impatrq/Pleper/Documentos Proyecto/CV Alumnos/CV Santiago_Alejandro_Tejeda.pdf

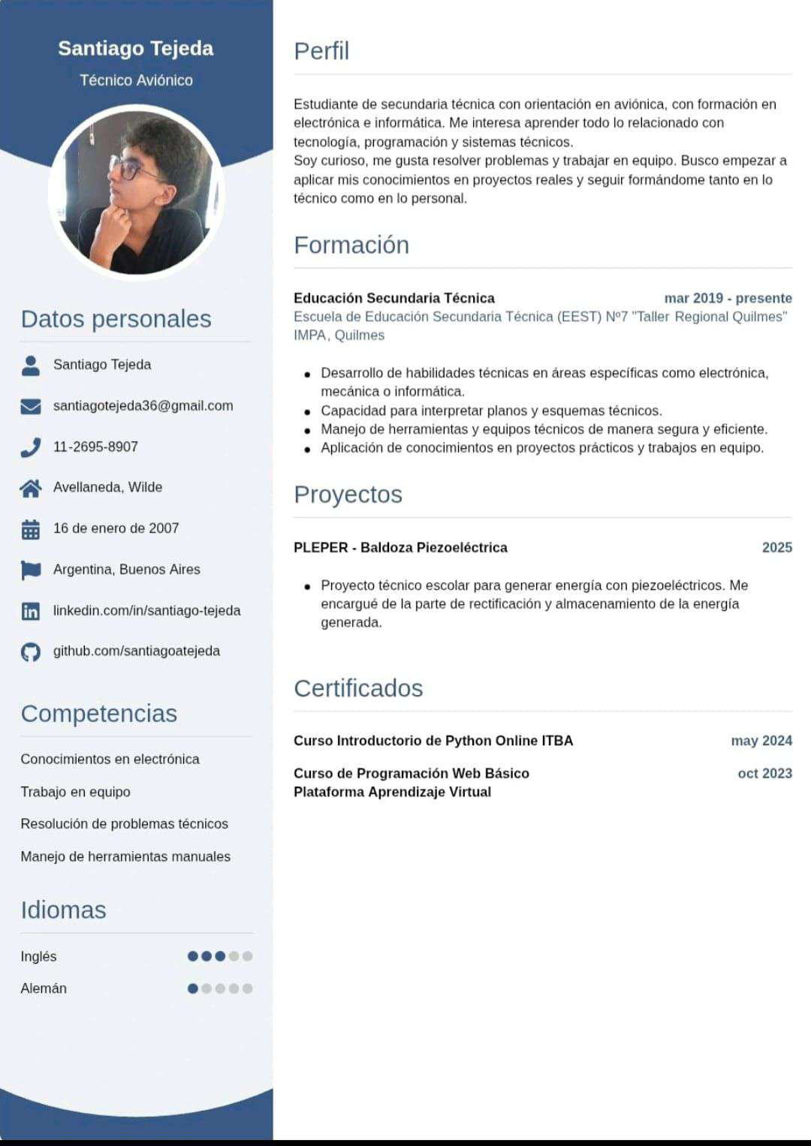
[picture p9: page 1]
