impatrq/Pleper/Documentos Proyecto/CV Alumnos/CV Ignacio Garcia Louzan.pdf

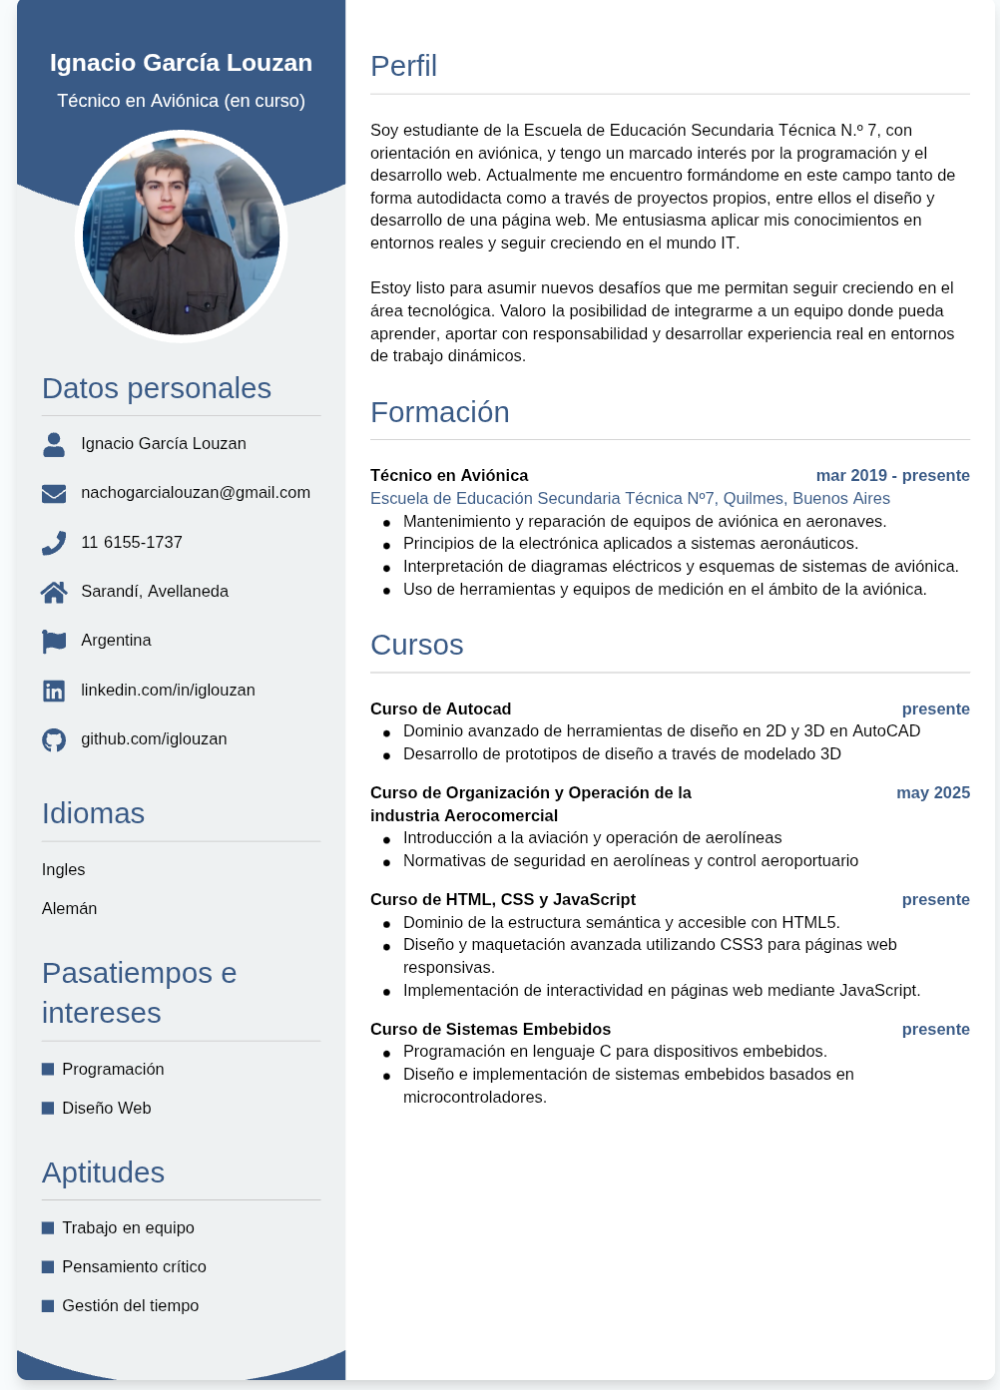
[picture p10: page 1]
