impatrq/Pleper/Diseño de placas/Diseño 3D/Banco de Capacitores Vista 1.png

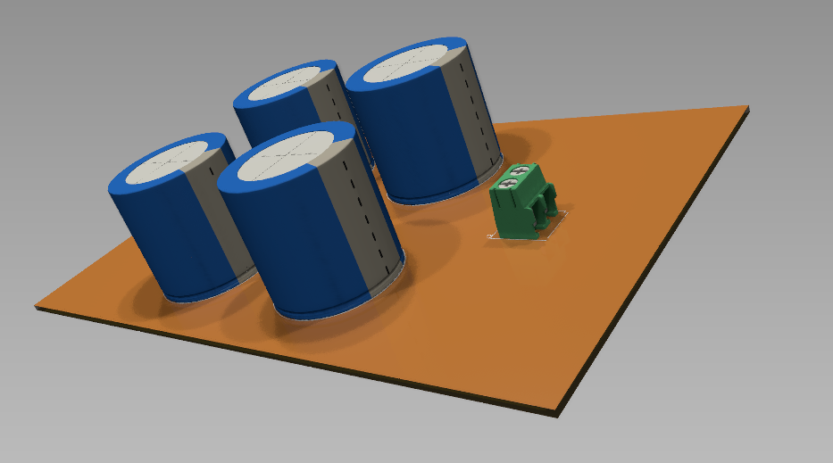
Diseño de placas/Diseño 3D/Banco de Capacitores Vista 1.png
