impatrq/Pleper/Diseño de placas/Diseño 3D/Banco de Capacitores Vista 3.png

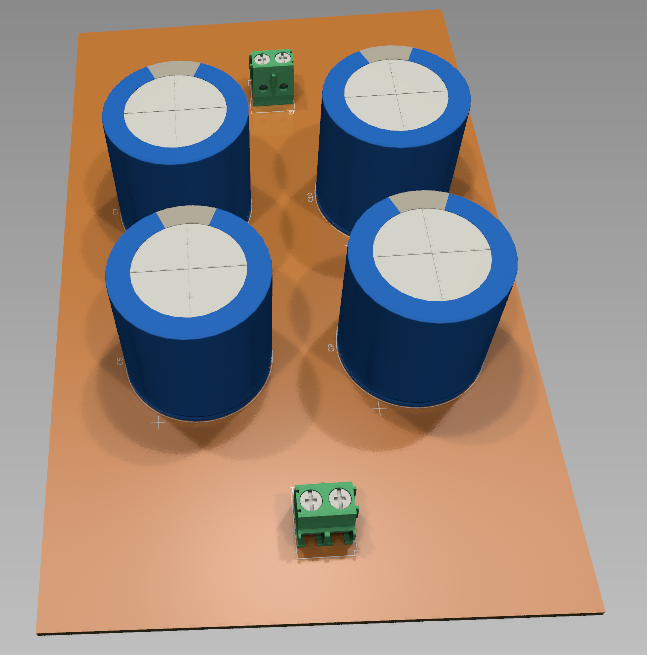
Diseño de placas/Diseño 3D/Banco de Capacitores Vista 3.png
