impatrq/Pleper/Diseño de placas/Diseño 3D/Placa rectificadora Vista 3.png

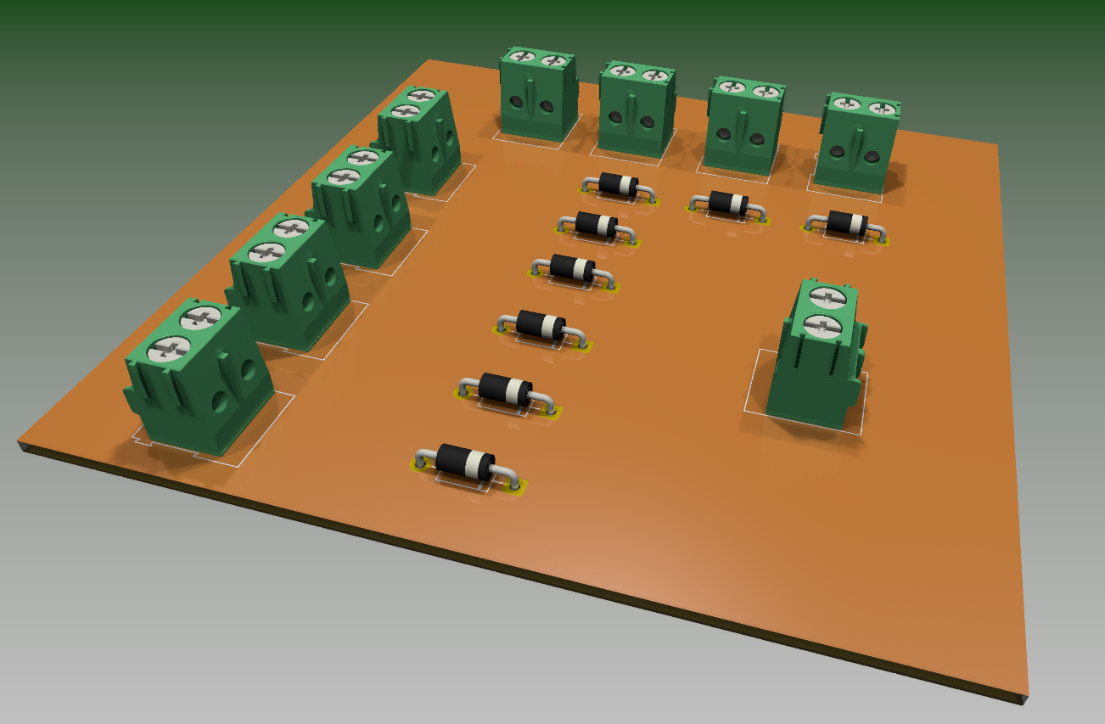
Diseño de placas/Diseño 3D/Placa rectificadora Vista 3.png
