impatrq/Pleper/Diseño de placas/Placa rectificadora/Boceto de rectificadora/20250923_140442.jpg

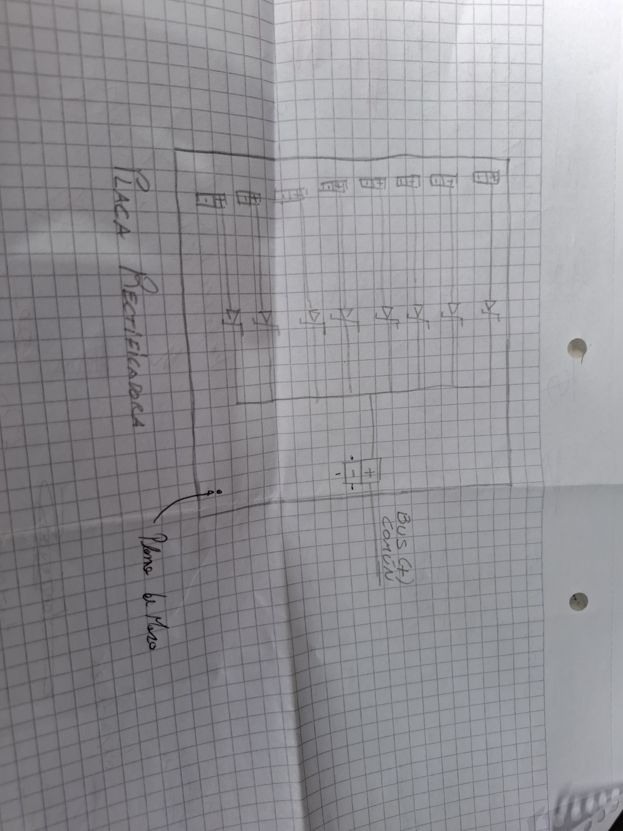
Diseño de placas/Placa rectificadora/Boceto de rectificadora/20250923_140442.jpg
