impatrq/Pleper/Diseño de placas/Placa rectificadora/Boceto de rectificadora/Esquematico placa rectificadora.png

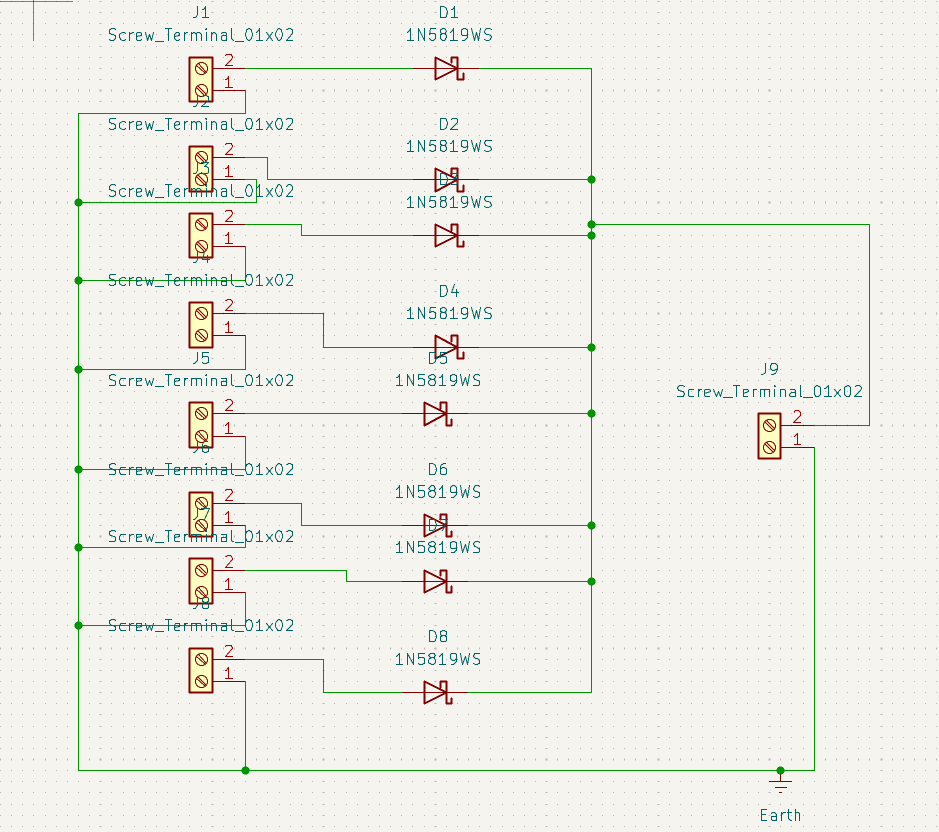
Diseño de placas/Placa rectificadora/Boceto de rectificadora/Esquematico placa rectificadora.png
