impatrq/Pleper/Diseño y modelos 3D/Imagenes de AutoCad/Captura de pantalla 2025-10-30 134244.png

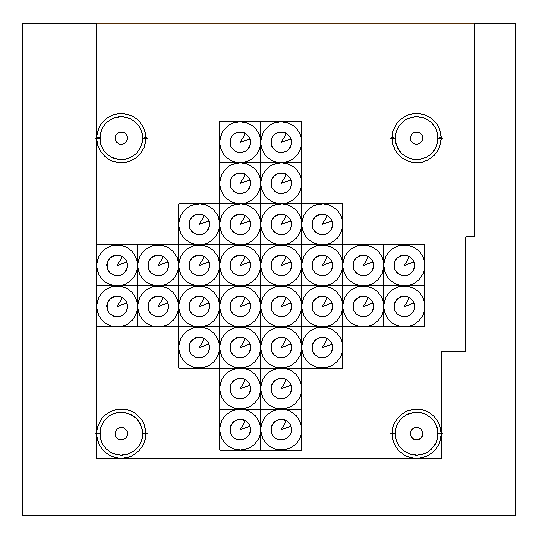
Diseño y modelos 3D/Imagenes de AutoCad/Captura de pantalla 2025-10-30 134244.png
