impatrq/Pleper/Diseño y modelos 3D/Imagenes de AutoCad/Vista conceptual 1.png

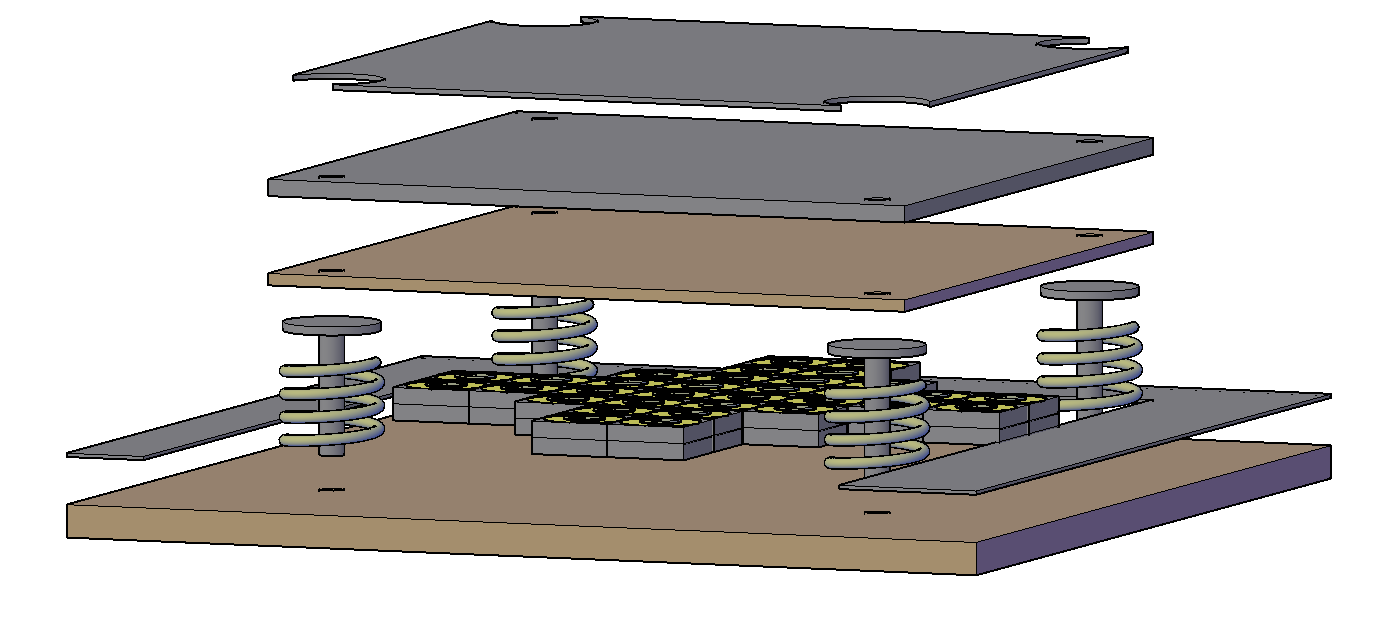
Diseño y modelos 3D/Imagenes de AutoCad/Vista conceptual 1.png
