impatrq/Pleper/Diseño y modelos 3D/Imagenes de AutoCad/Vista conceptual 5.png

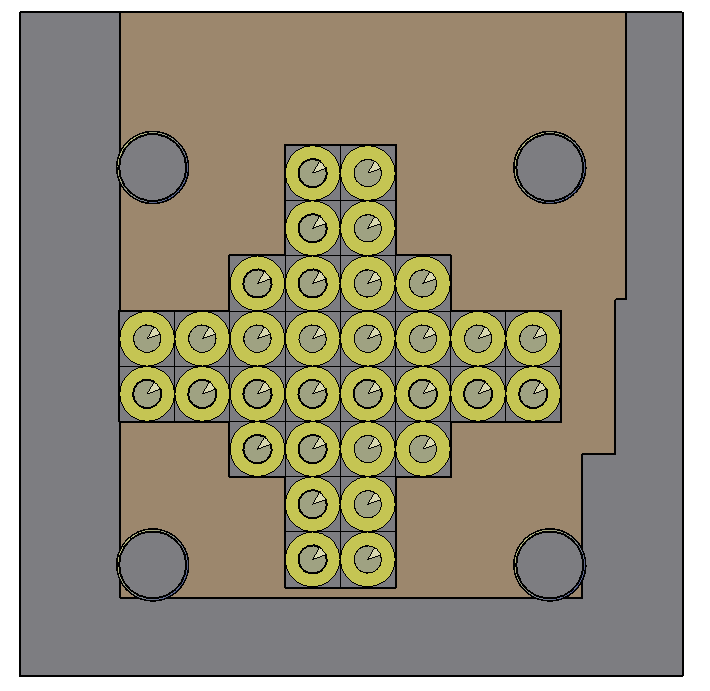
Diseño y modelos 3D/Imagenes de AutoCad/Vista conceptual 5.png
