impatrq/Pleper/Diseño y modelos 3D/Imagenes de AutoCad/Vista Isométrica 2.png

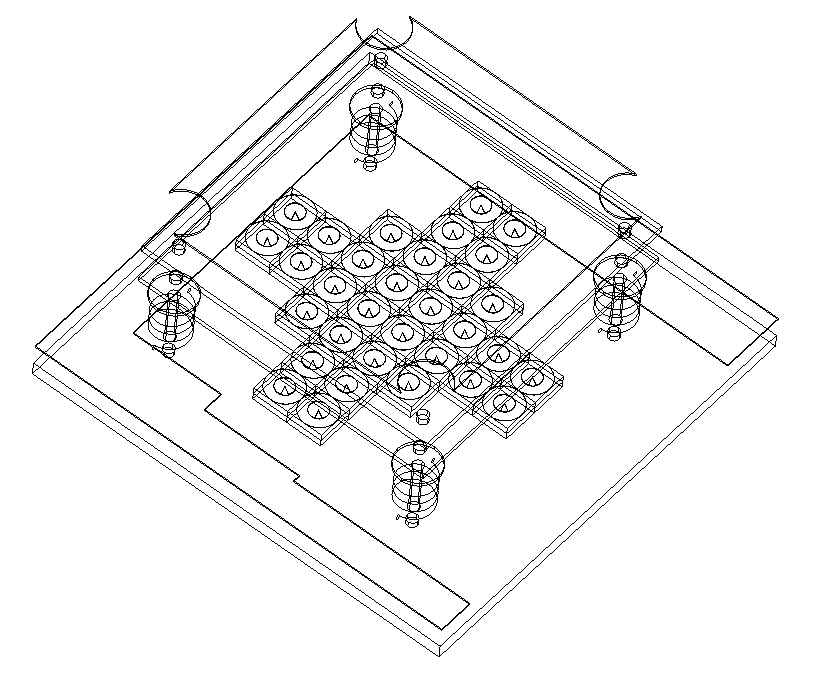
Diseño y modelos 3D/Imagenes de AutoCad/Vista Isométrica 2.png
