impatrq/Pleper/Diseño y modelos 3D/Imagenes de AutoCad/Vista Isométrica 3.png

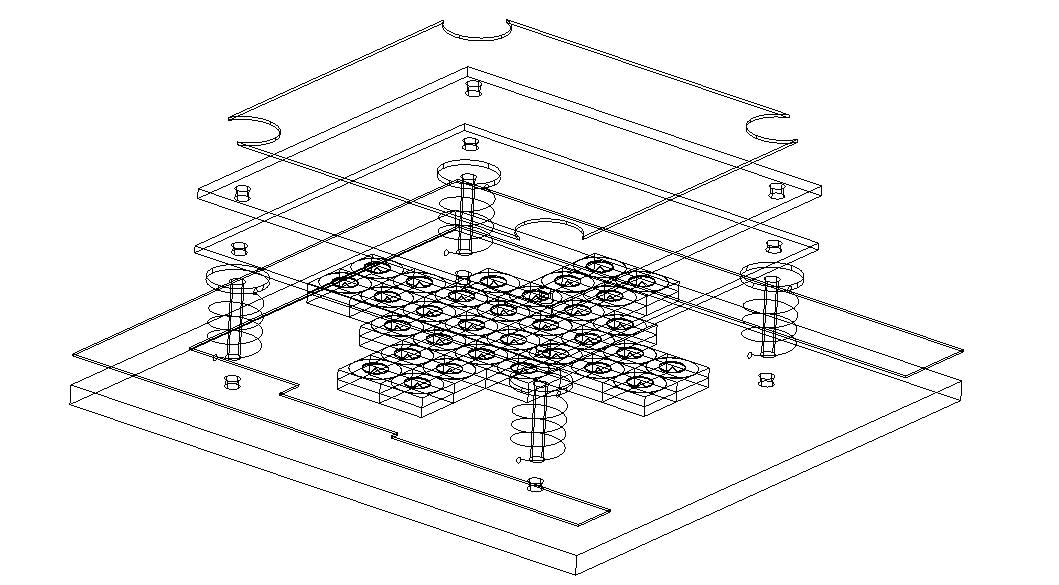
Diseño y modelos 3D/Imagenes de AutoCad/Vista Isométrica 3.png
