impatrq/Pleper/Diseño y modelos 3D/Imagenes de AutoCad/Vista Isométrica prototipo.png

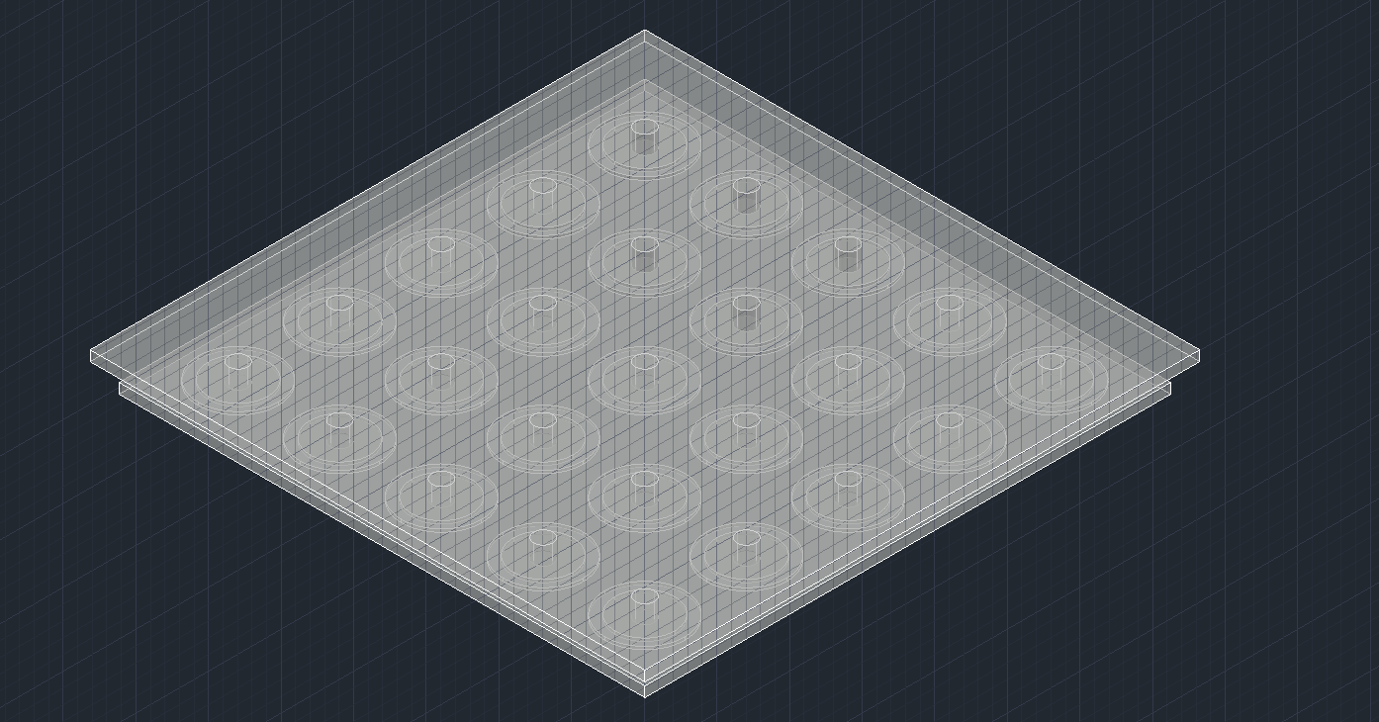
Diseño y modelos 3D/Imagenes de AutoCad/Vista Isométrica prototipo.png
