impatrq/Pleper/Diseño y modelos 3D/Imagenes de AutoCad/Vista realista 4.png

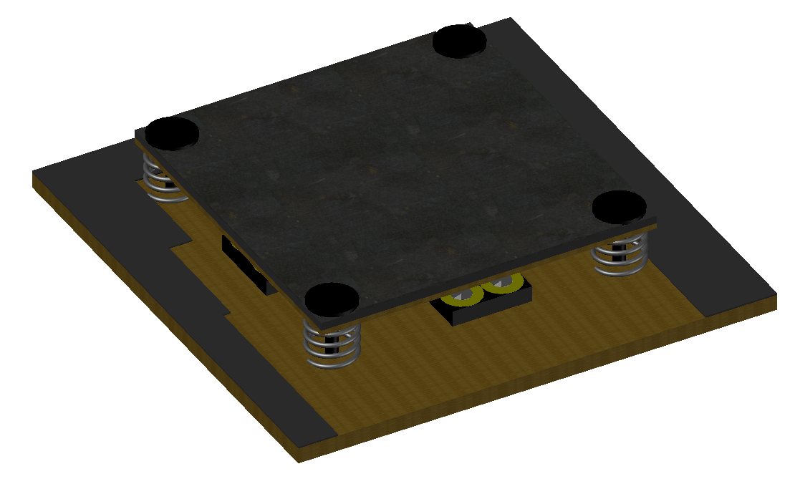
Diseño y modelos 3D/Imagenes de AutoCad/Vista realista 4.png
