impatrq/Pleper/Diseño y modelos 3D/Imagenes de AutoCad/Vista realista 5.png

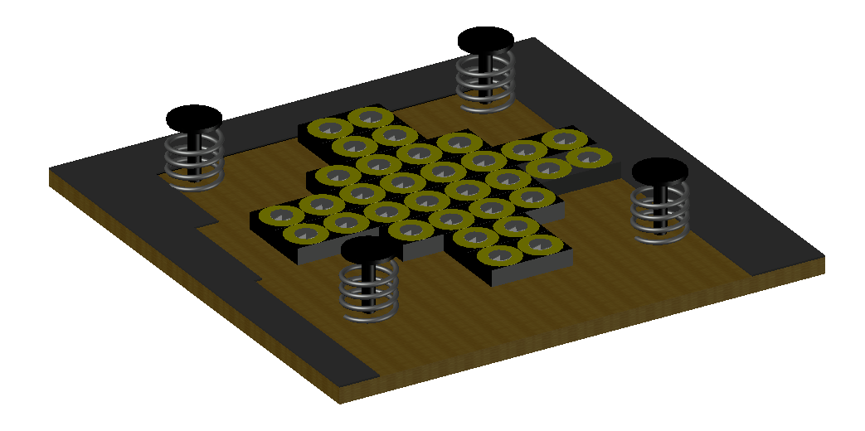
Diseño y modelos 3D/Imagenes de AutoCad/Vista realista 5.png
