impatrq/Pleper/Diseño y modelos 3D/Imagenes de AutoCad/Vista realista.png

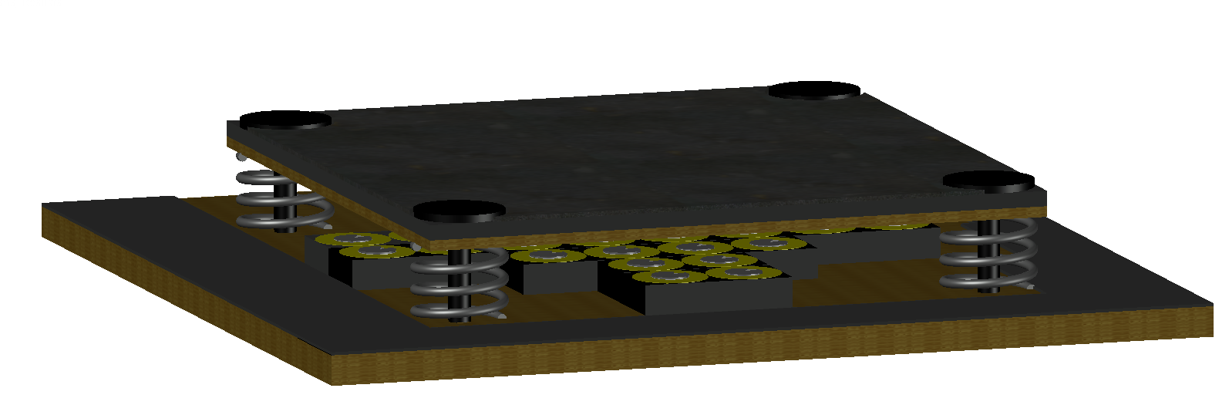
Diseño y modelos 3D/Imagenes de AutoCad/Vista realista.png
