impatrq/Pleper/Diseño y modelos 3D/Imagenes de AutoCad/Vista Superior prototipo.png

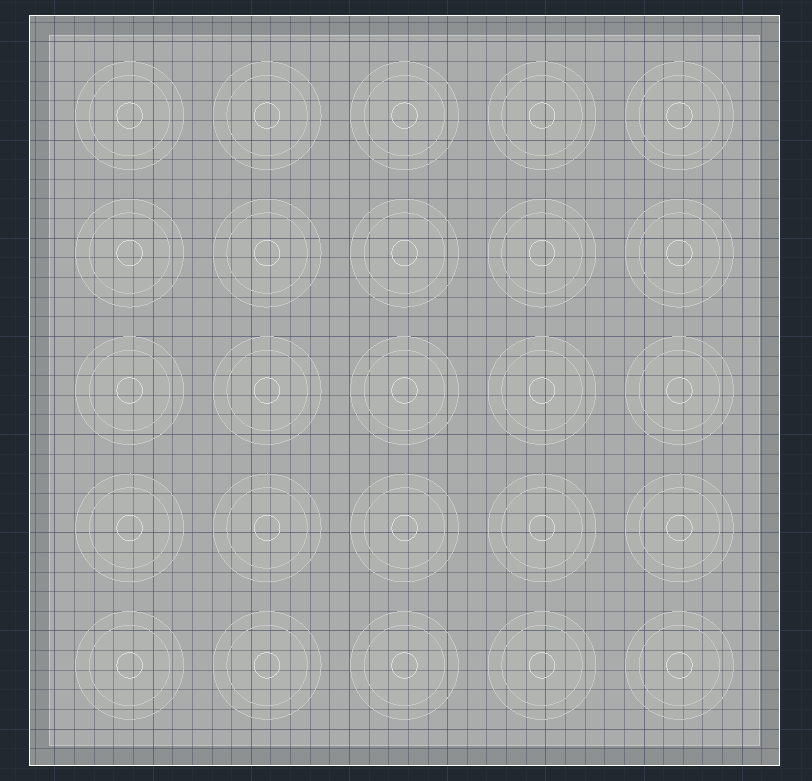
Diseño y modelos 3D/Imagenes de AutoCad/Vista Superior prototipo.png
