impatrq/Pleper/Documentos Proyecto/Video de presentacion/Pisada en prototipo de placa.jpg

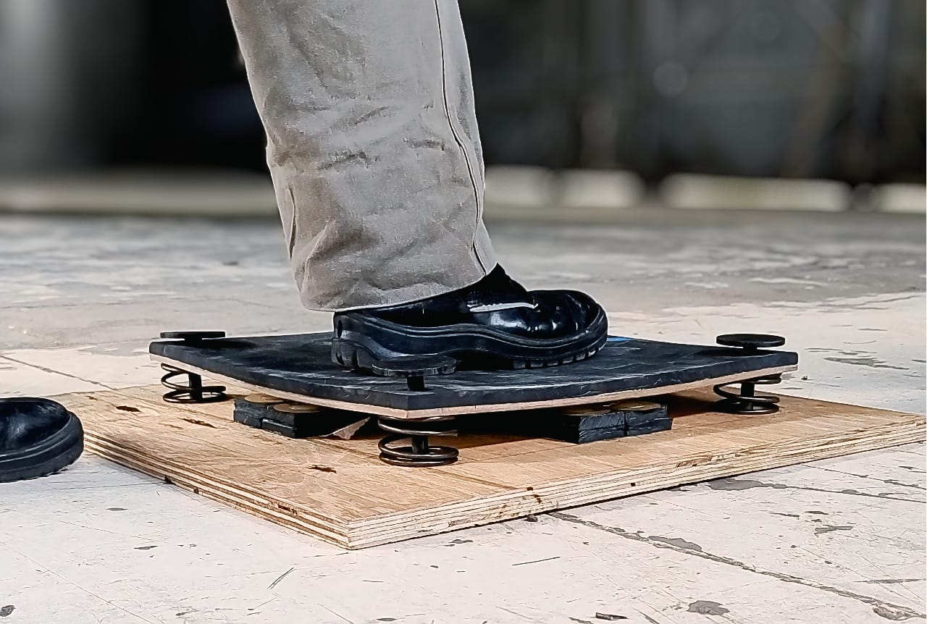
Documentos Proyecto/Video de presentacion/Pisada en prototipo de placa.jpg
