impatrq/Pleper/img/fondo.jpg

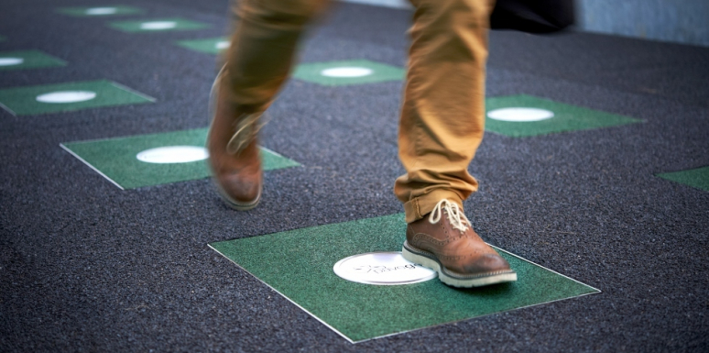
img/fondo.jpg
