impatrq/Pleper/Imágenes Proyecto/Desarrollo/Circuitos/Investigación sobre el circuito de bombeo por carga capacitiva.jpg

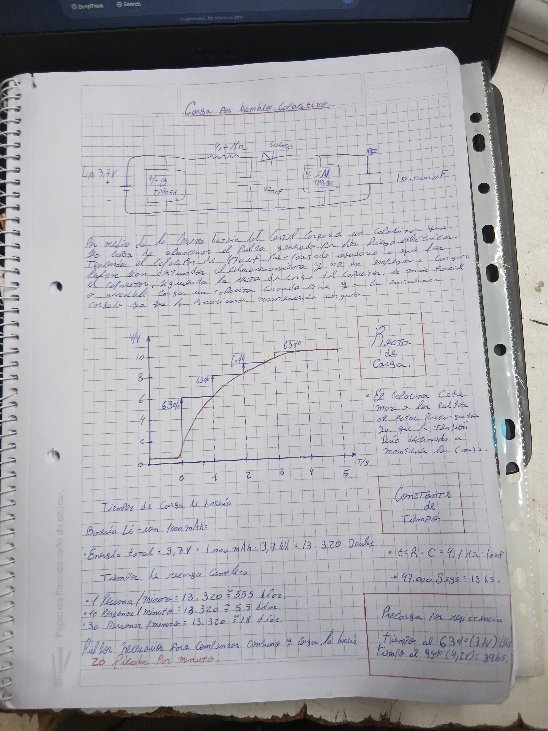
Imágenes Proyecto/Desarrollo/Circuitos/Investigación sobre el circuito de bombeo por carga capacitiva.jpg
