impatrq/Pleper/Imágenes Proyecto/Desarrollo/Circuitos/Primera Versión.jpg

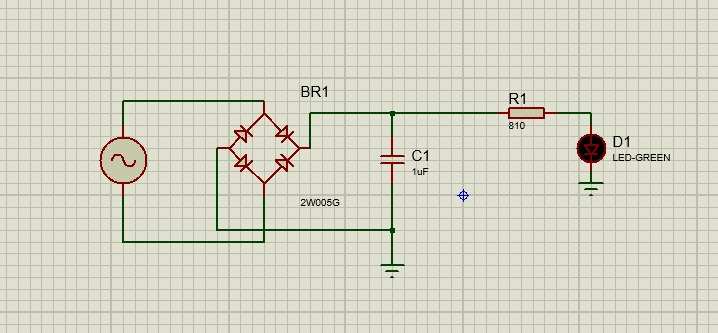
Imágenes Proyecto/Desarrollo/Circuitos/Primera Versión.jpg
