impatrq/Pleper/Imágenes Proyecto/Desarrollo/Circuitos/Simulación seis piezoeléctricos.jpg

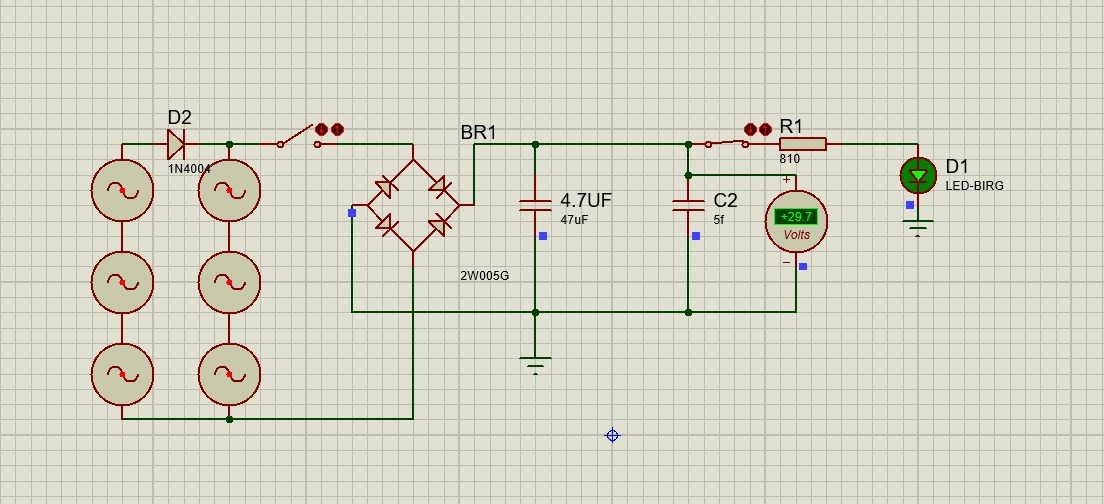
Imágenes Proyecto/Desarrollo/Circuitos/Simulación seis piezoeléctricos.jpg
