impatrq/Pleper/Imágenes Proyecto/Desarrollo/Circuitos/Simulación un piezoeléctrico con rectificación.jpg

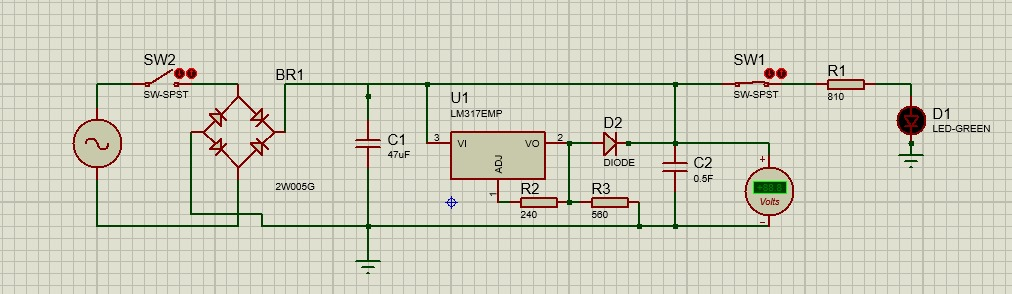
Imágenes Proyecto/Desarrollo/Circuitos/Simulación un piezoeléctrico con rectificación.jpg
