impatrq/Pleper/Imágenes Proyecto/Desarrollo/Imagen de placas/Banco de capacitores PCB.png

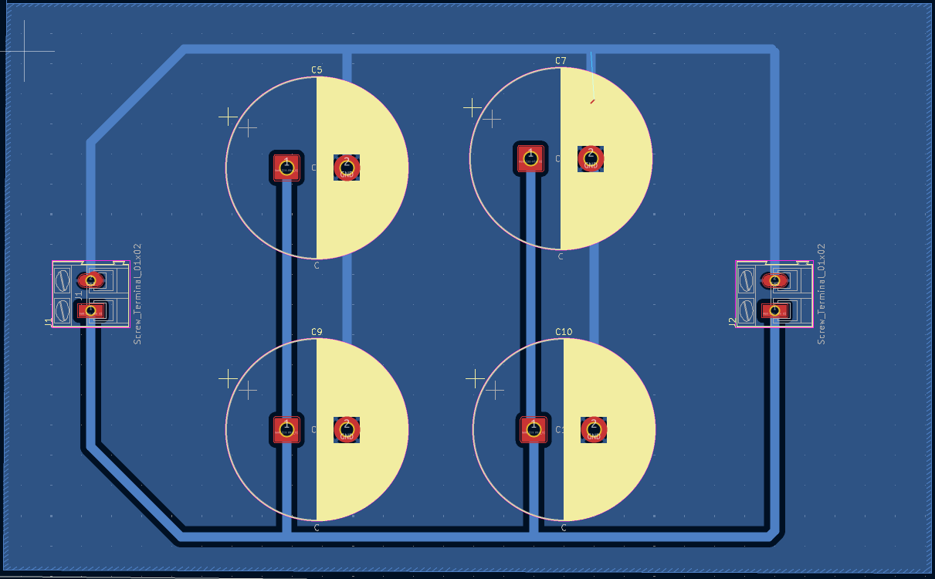
Imágenes Proyecto/Desarrollo/Imagen de placas/Banco de capacitores PCB.png
