impatrq/Pleper/Imágenes Proyecto/Desarrollo/Imagen de placas/Banco de capacitores.jpg

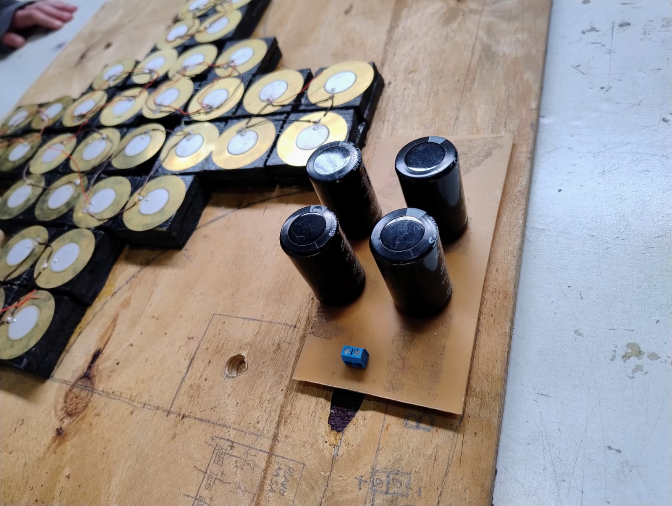
Imágenes Proyecto/Desarrollo/Imagen de placas/Banco de capacitores.jpg
