impatrq/Pleper/Imágenes Proyecto/Desarrollo/Imagen de placas/Banco de capacitores.png

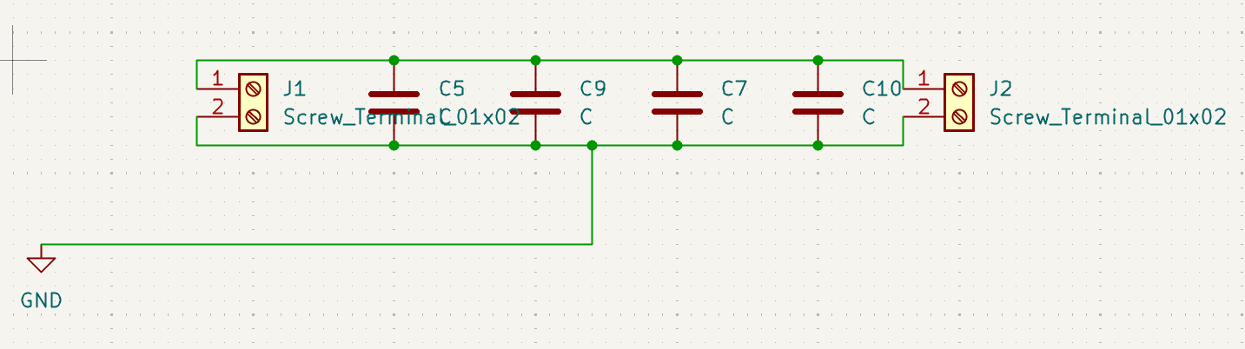
Imágenes Proyecto/Desarrollo/Imagen de placas/Banco de capacitores.png
