impatrq/Pleper/Imágenes Proyecto/Desarrollo/Imagen de placas/Circuito de la baldosa de carga por bombeo capacitivo.jpg

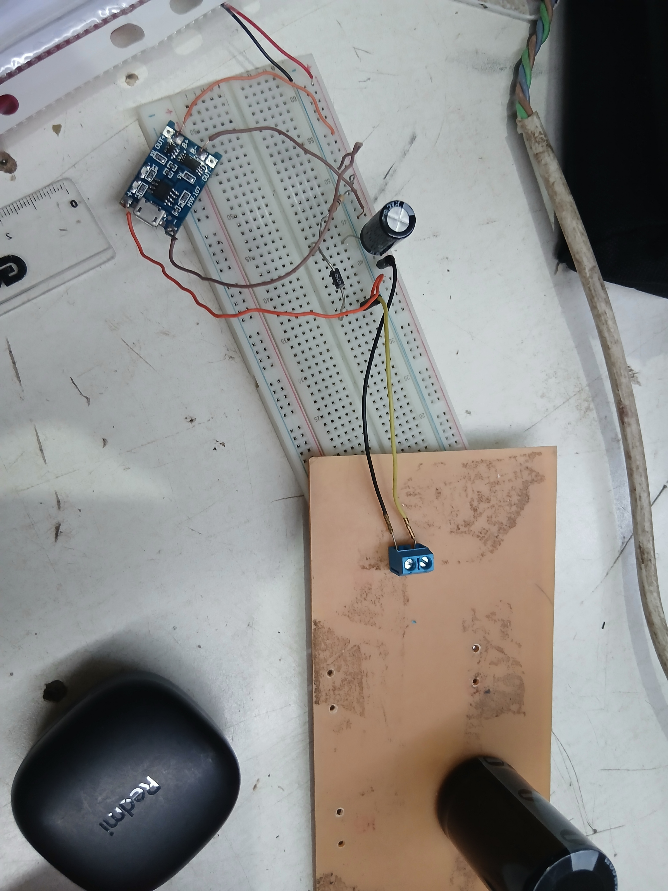
Imágenes Proyecto/Desarrollo/Imagen de placas/Circuito de la baldosa de carga por bombeo capacitivo.jpg
