impatrq/Pleper/Imágenes Proyecto/Desarrollo/Imagen de placas/Placa rectificadora PCB.png

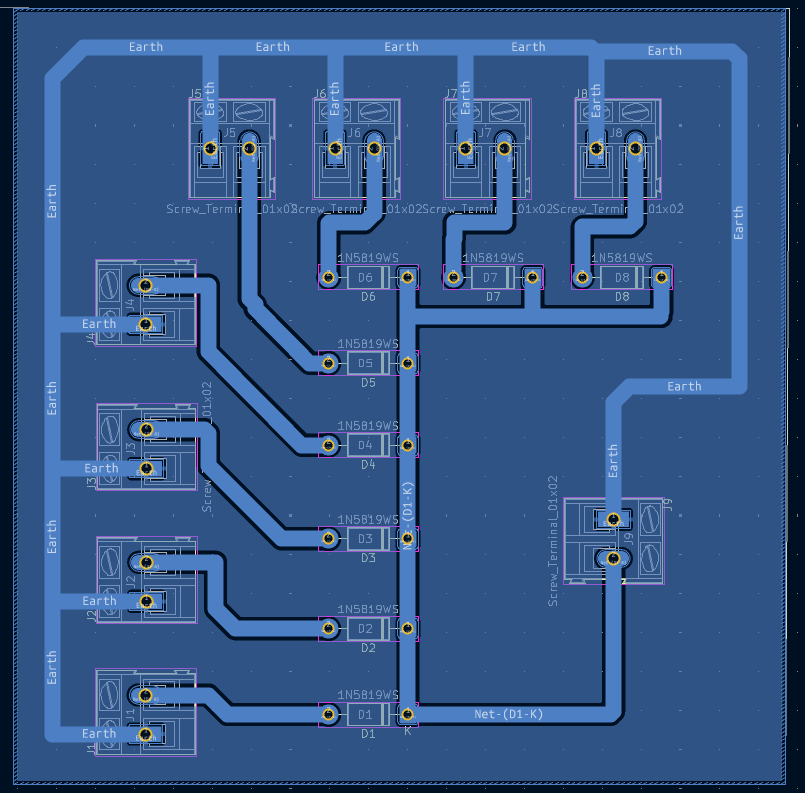
Imágenes Proyecto/Desarrollo/Imagen de placas/Placa rectificadora PCB.png
