impatrq/Pleper/Imágenes Proyecto/Desarrollo/Mediciones/Medicion de 1 tope en un grupo.jpeg

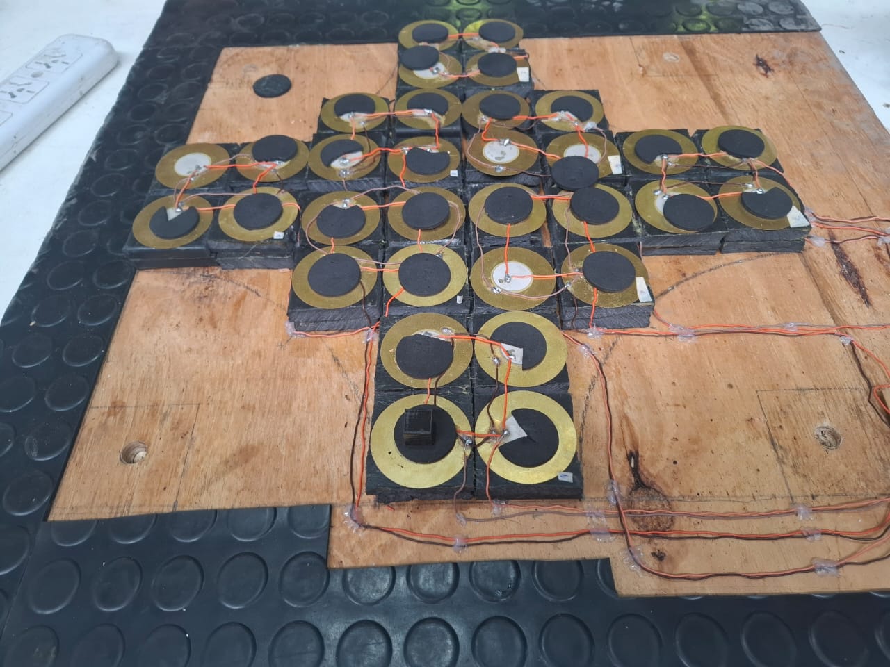
Imágenes Proyecto/Desarrollo/Mediciones/Medicion de 1 tope en un grupo.jpeg
