impatrq/Pleper/Imágenes Proyecto/Desarrollo/Mediciones/Medicion de 2  topes en un grupo.jpeg

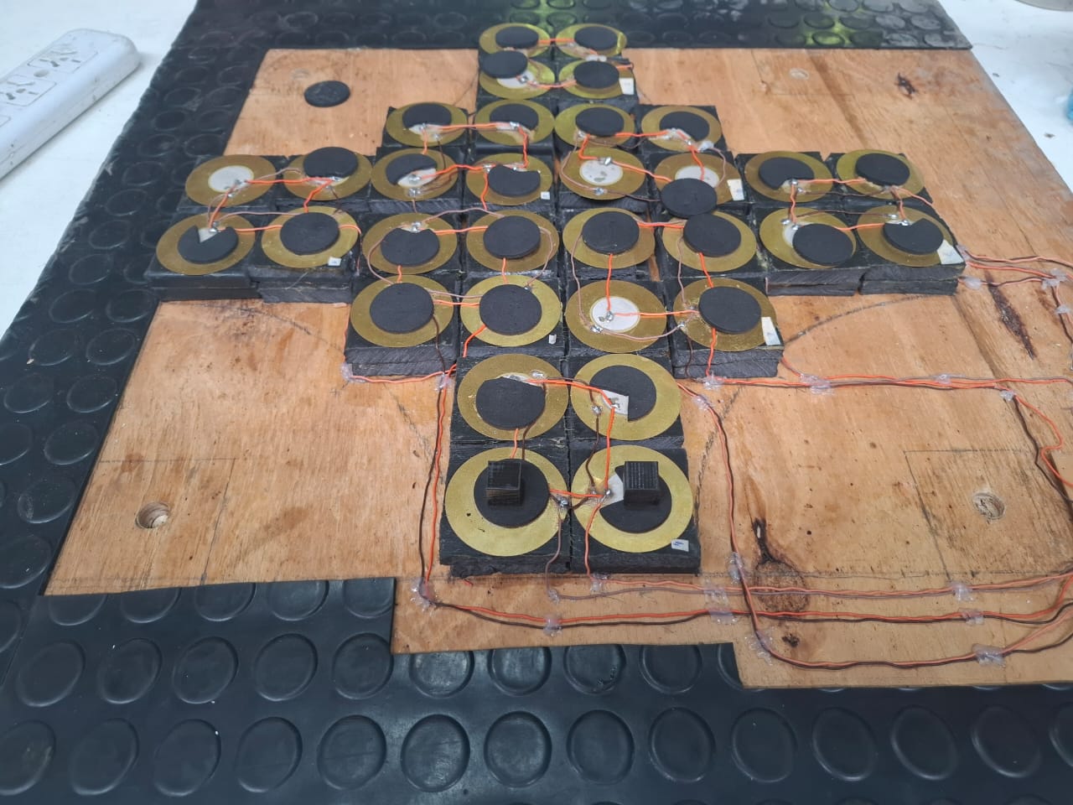
Imágenes Proyecto/Desarrollo/Mediciones/Medicion de 2 topes en un grupo.jpeg
