impatrq/Pleper/Imágenes Proyecto/Desarrollo/Mediciones/Medicion de 3 topes en un grupo.jpeg

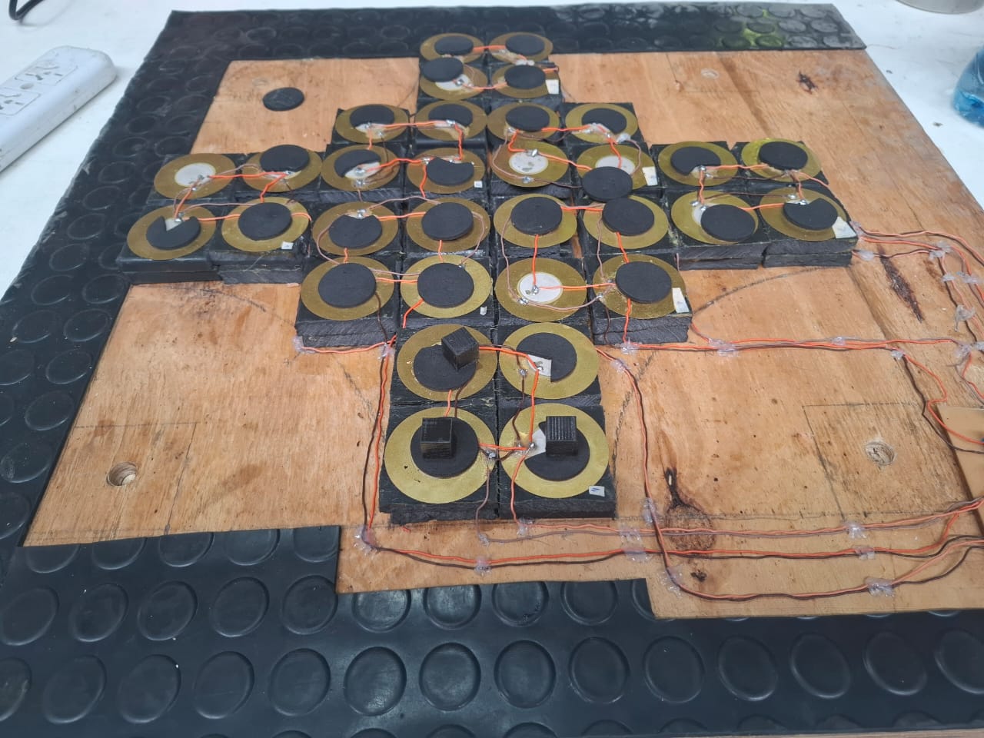
Imágenes Proyecto/Desarrollo/Mediciones/Medicion de 3 topes en un grupo.jpeg
