impatrq/Pleper/Imágenes Proyecto/Desarrollo/Mediciones/Medicion de 4 topes en un grupo.jpeg

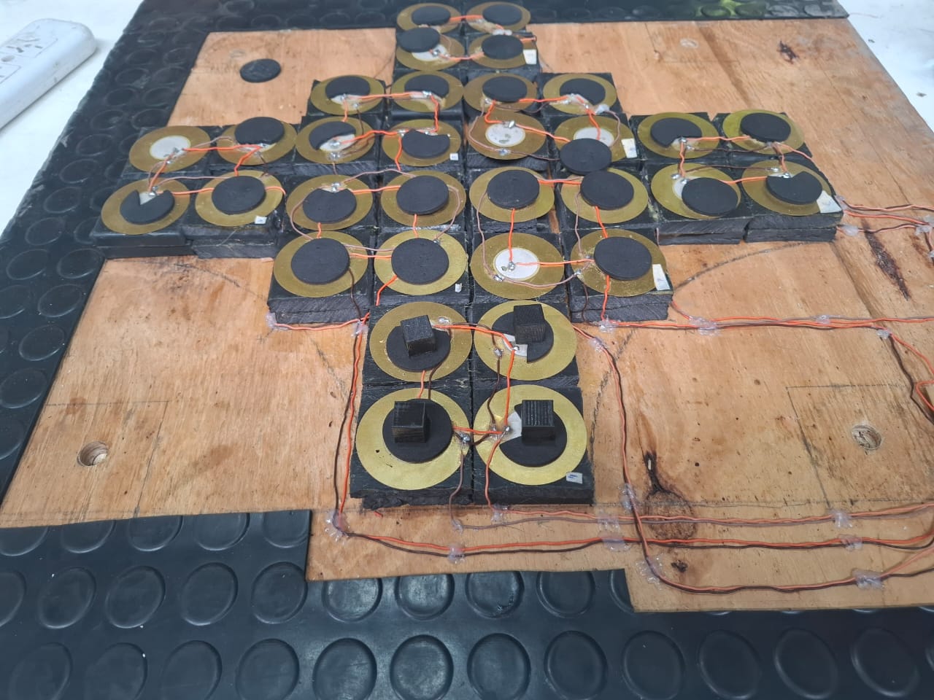
Imágenes Proyecto/Desarrollo/Mediciones/Medicion de 4 topes en un grupo.jpeg
