impatrq/Pleper/Imágenes Proyecto/Desarrollo/Mediciones/Medicion de un tope en cada esquina.jpeg

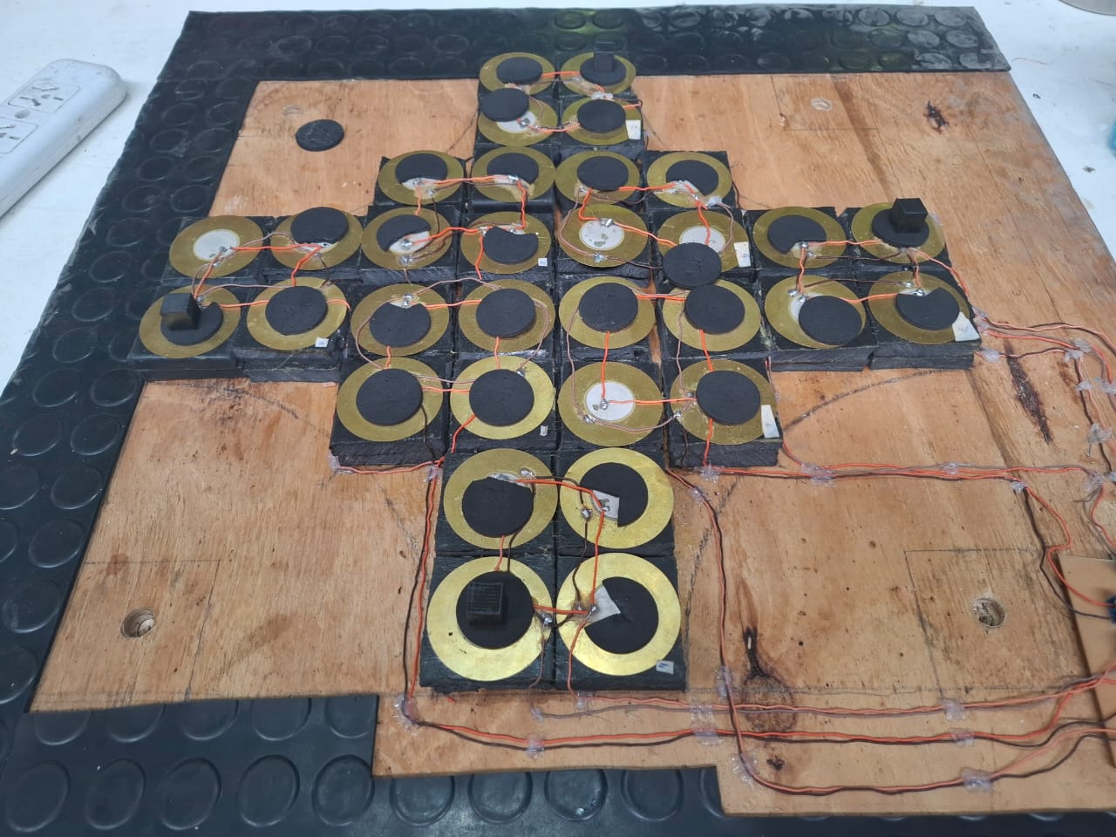
Imágenes Proyecto/Desarrollo/Mediciones/Medicion de un tope en cada esquina.jpeg
