impatrq/Pleper/Imágenes Proyecto/Desarrollo/Mediciones/Medicion del corte de alfombra de caucho para los topes.jpg

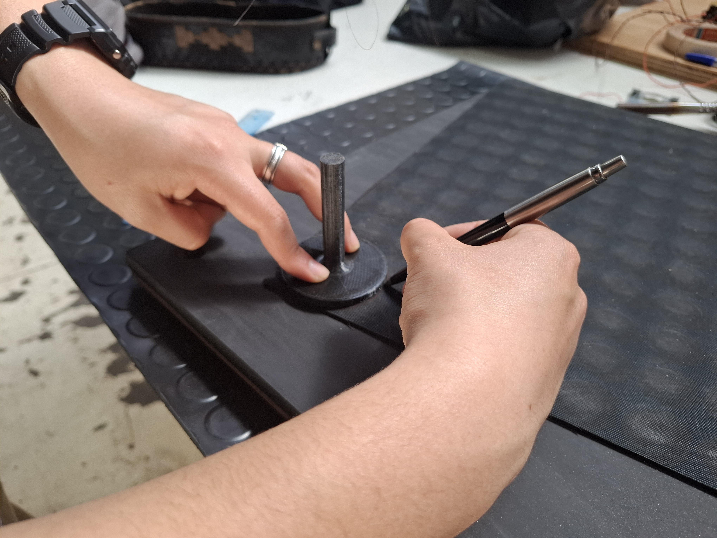
Imágenes Proyecto/Desarrollo/Mediciones/Medicion del corte de alfombra de caucho para los topes.jpg
