impatrq/Pleper/Imágenes Proyecto/Desarrollo/Mediciones/Mediciones en el prototipo.jpg

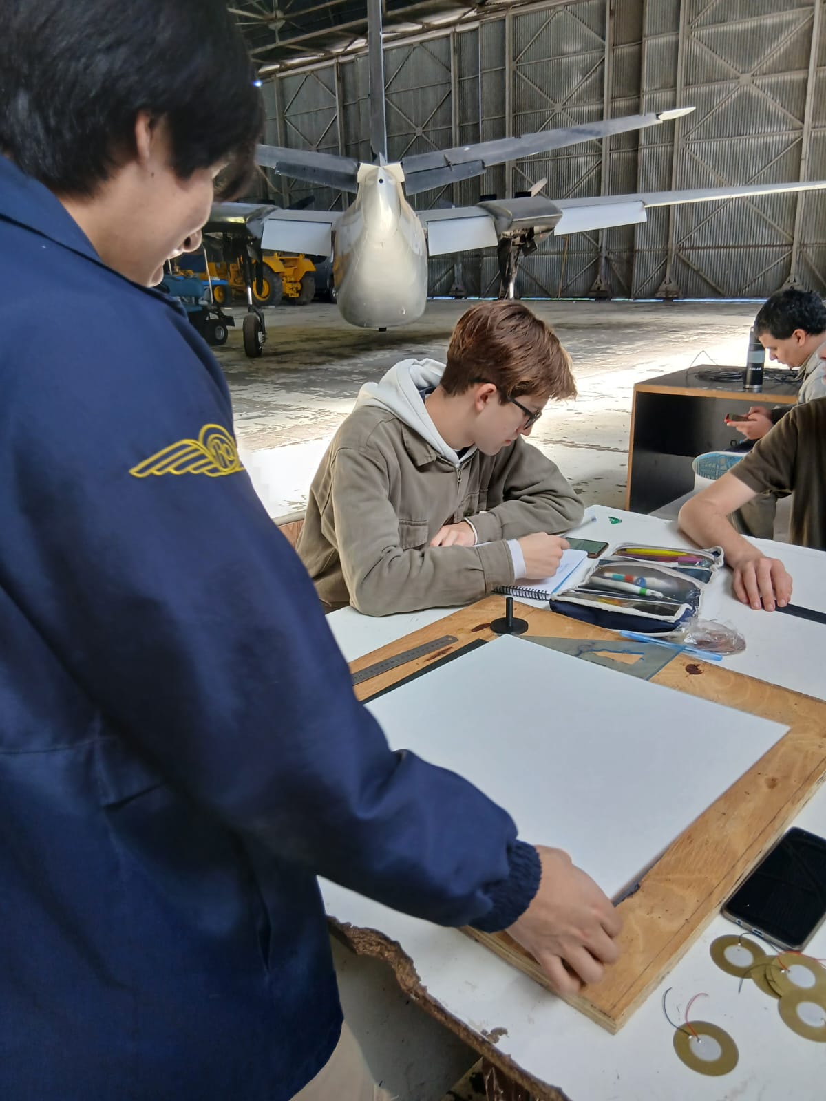
Imágenes Proyecto/Desarrollo/Mediciones/Mediciones en el prototipo.jpg
