impatrq/Pleper/Imágenes Proyecto/Desarrollo/Mediciones/Medición de los resortes.jpg

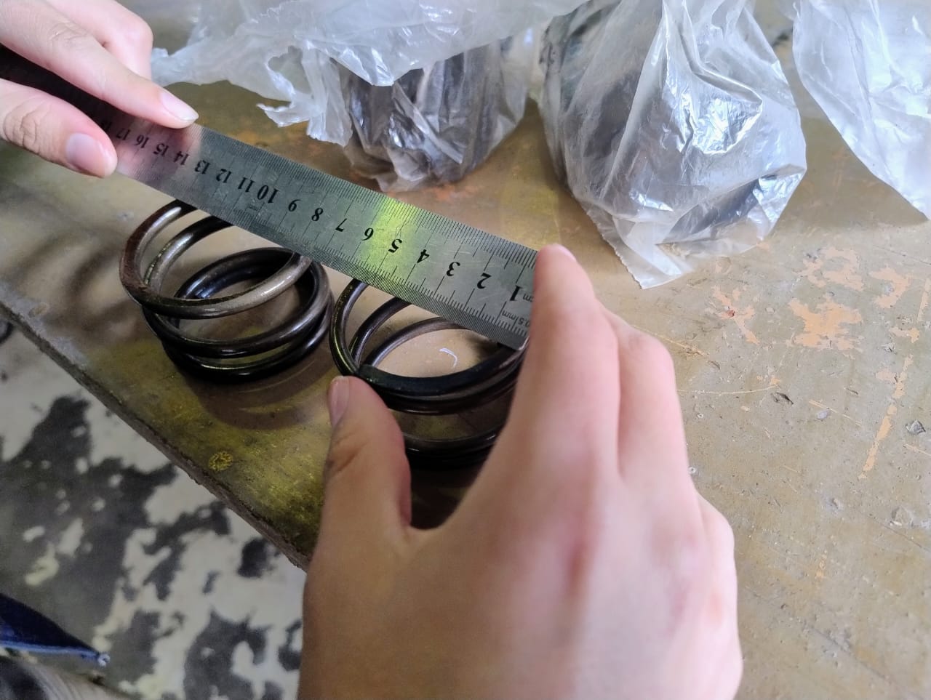
Imágenes Proyecto/Desarrollo/Mediciones/Medición de los resortes.jpg
