impatrq/Pleper/Imágenes Proyecto/Desarrollo/Mediciones/Medición del tiempo de los pulsos de la baldosa.jpg

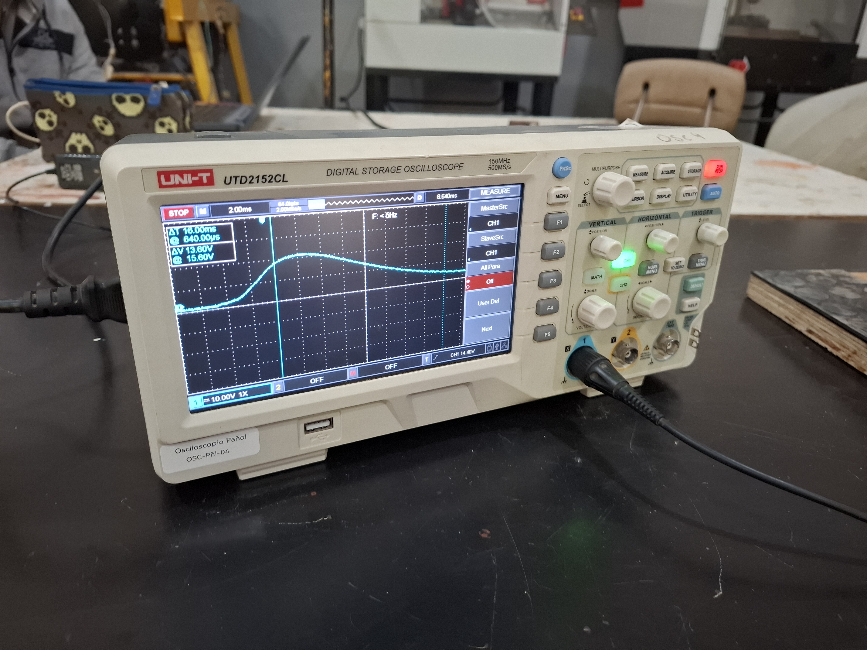
Imágenes Proyecto/Desarrollo/Mediciones/Medición del tiempo de los pulsos de la baldosa.jpg
