impatrq/Pleper/Imágenes Proyecto/Desarrollo/Mediciones/Medición Piezoeléctrico con Osciloscopio Conexión.jpg

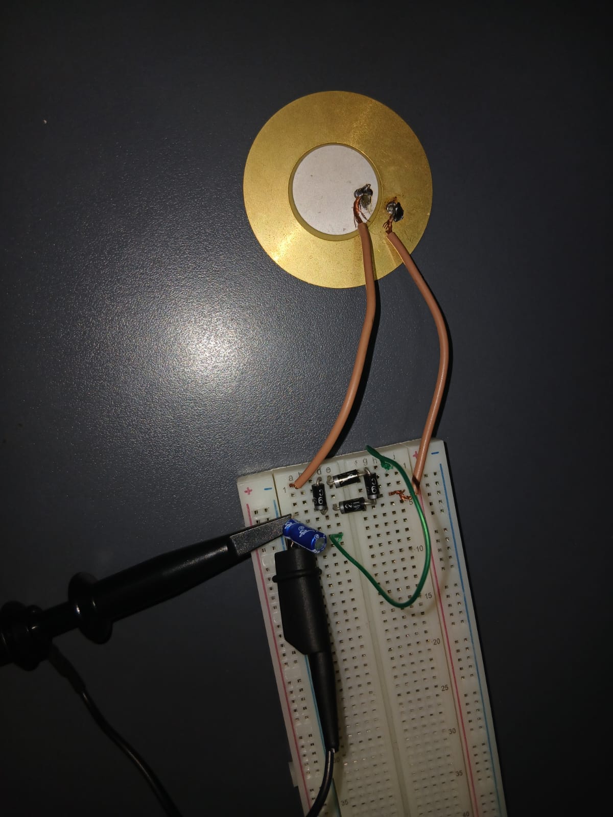
Imágenes Proyecto/Desarrollo/Mediciones/Medición Piezoeléctrico con Osciloscopio Conexión.jpg
