impatrq/Pleper/Imágenes Proyecto/Desarrollo/Mediciones/Medición piezoeléctricos sobre la baldosa.jpg

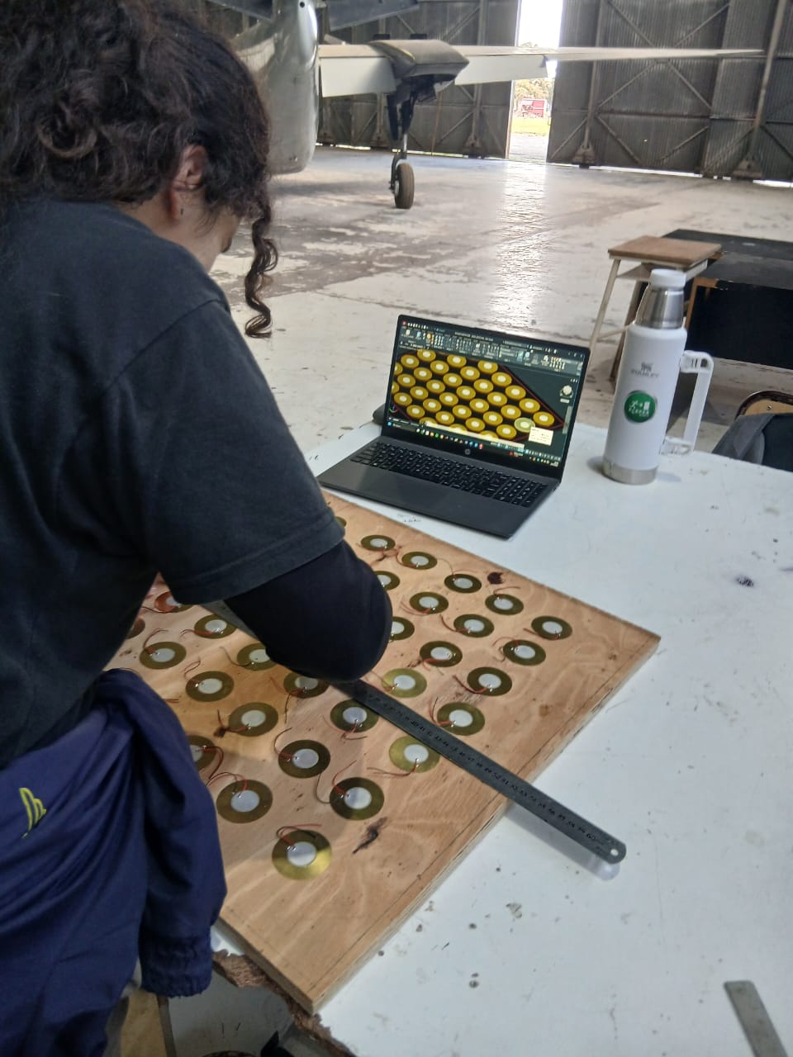
Imágenes Proyecto/Desarrollo/Mediciones/Medición piezoeléctricos sobre la baldosa.jpg
