impatrq/Pleper/Imágenes Proyecto/Desarrollo/Mediciones/Medir la alfombra antideslizante.jpg

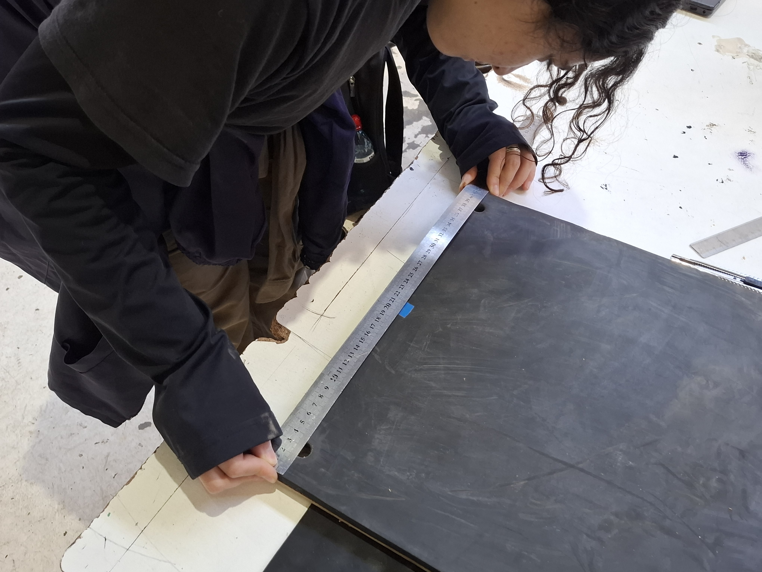
Imágenes Proyecto/Desarrollo/Mediciones/Medir la alfombra antideslizante.jpg
