impatrq/Pleper/Imágenes Proyecto/Desarrollo/Mediciones/Probando piezoelectricos para la medición.jpg

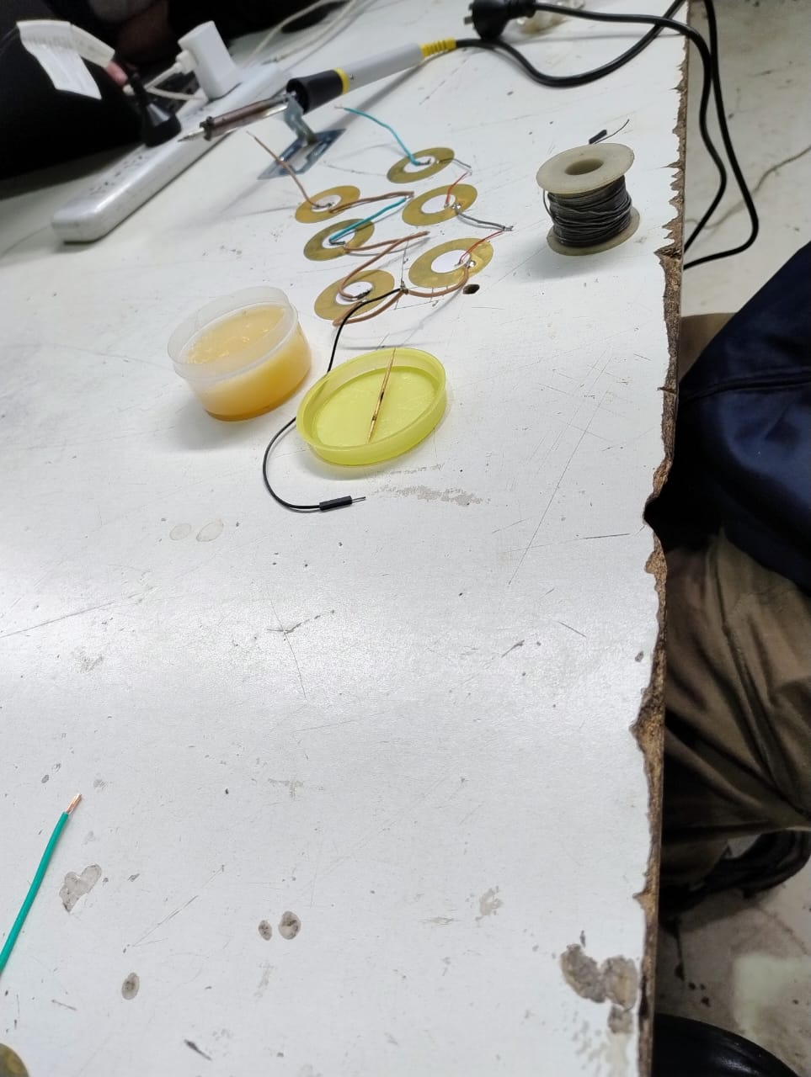
Imágenes Proyecto/Desarrollo/Mediciones/Probando piezoelectricos para la medición.jpg
