impatrq/Pleper/Imágenes Proyecto/Fotos grupales/DSC_0026.JPG

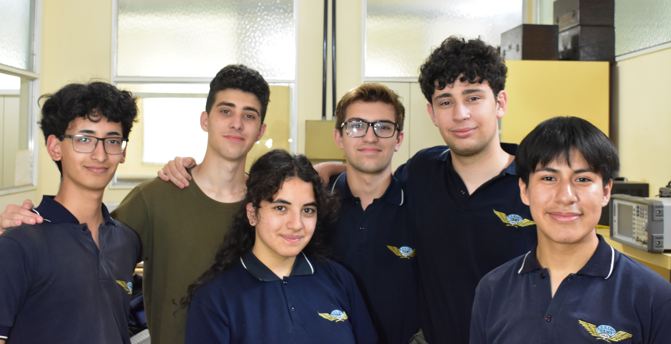
Imágenes Proyecto/Fotos grupales/DSC_0026.JPG
