impatrq/Pleper/Imágenes Proyecto/instagram/Banco de capacitores/Publicacion banco de capacitores.jpeg

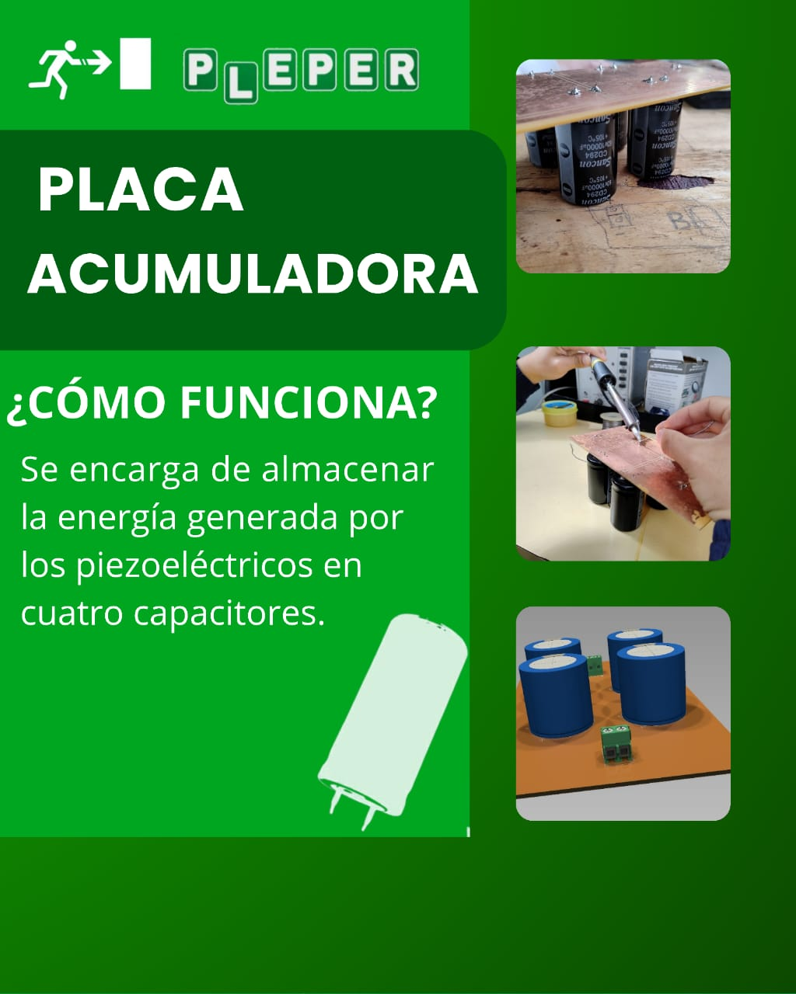
Imágenes Proyecto/instagram/Banco de capacitores/Publicacion banco de capacitores.jpeg
