impatrq/Pleper/Imágenes Proyecto/instagram/Placa Rectificadora/Publicacion placa rectificadora.jpeg

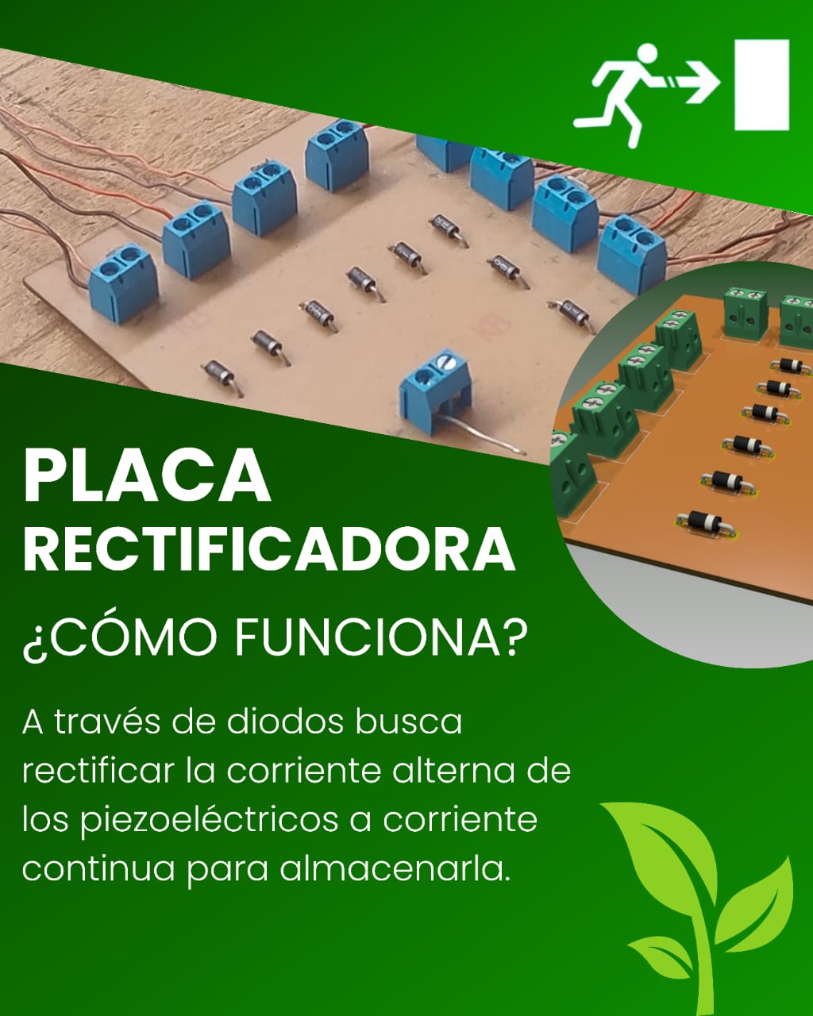
Imágenes Proyecto/instagram/Placa Rectificadora/Publicacion placa rectificadora.jpeg
