impatrq/Pleper/Imágenes Proyecto/instagram/Publicacion triple/Portada Almacenamiento.jpeg

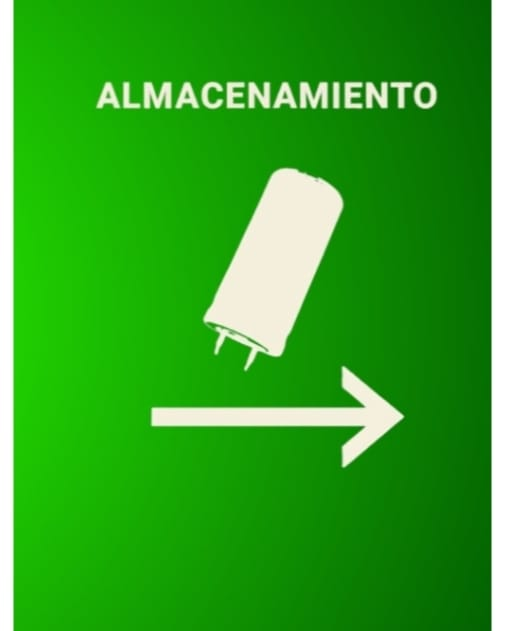
Imágenes Proyecto/instagram/Publicacion triple/Portada Almacenamiento.jpeg
