impatrq/Pleper/Imágenes Proyecto/instagram/Publicacion triple/Portada Estructura.jpeg

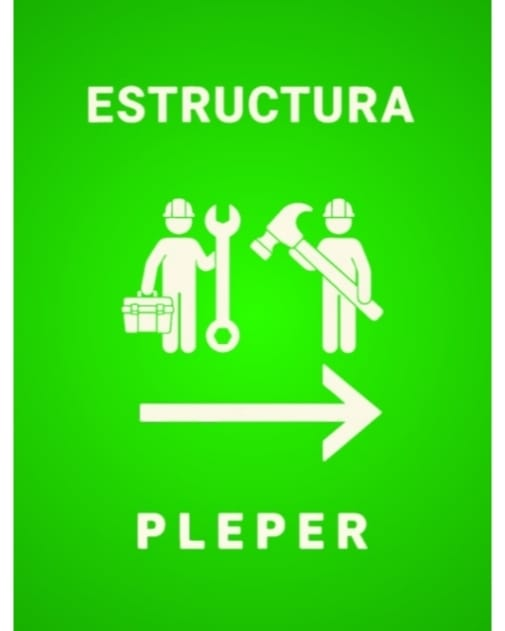
Imágenes Proyecto/instagram/Publicacion triple/Portada Estructura.jpeg
