impatrq/Pleper/Imágenes Proyecto/instagram/Publicacion triple/Portada Rectificadora.jpeg

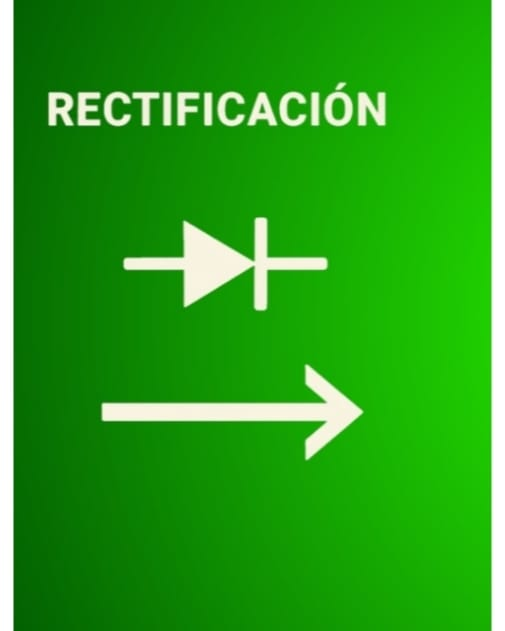
Imágenes Proyecto/instagram/Publicacion triple/Portada Rectificadora.jpeg
