impatrq/Pleper/Imágenes Proyecto/instagram/Publicacion triple/Portada triple de instagram.jpeg

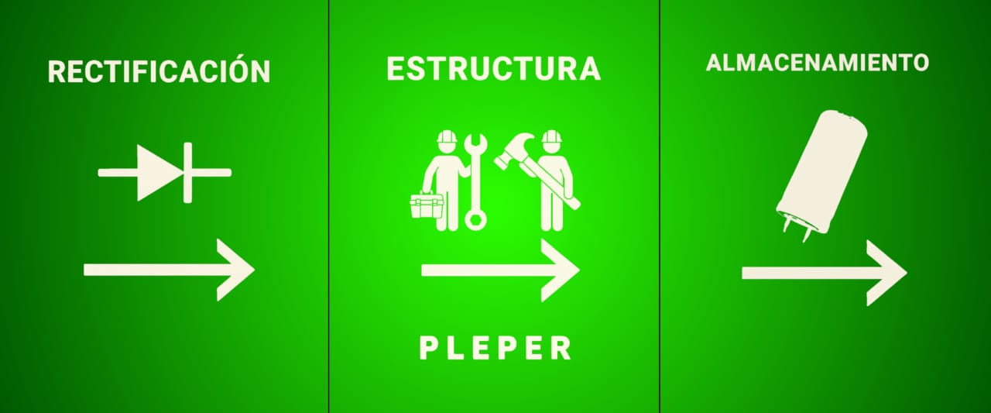
Imágenes Proyecto/instagram/Publicacion triple/Portada triple de instagram.jpeg
