impatrq/Pleper/Imágenes Proyecto/instagram/Publicación Feria/1.png

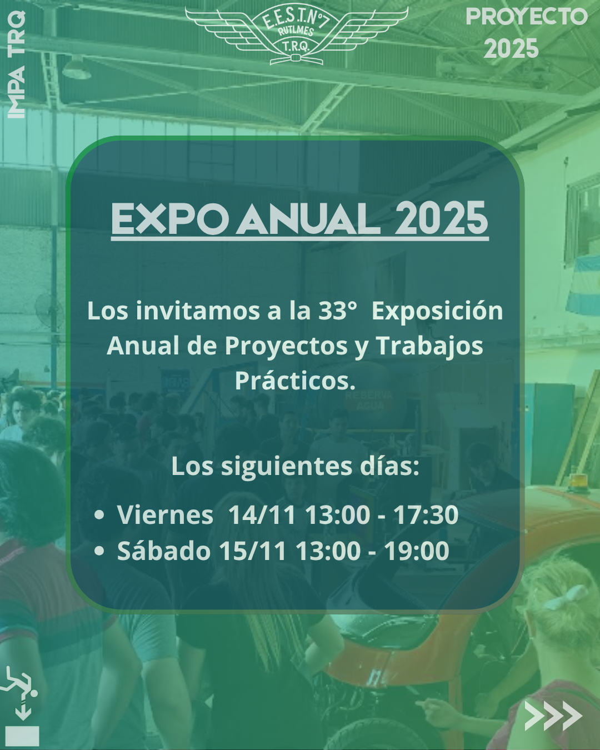
Imágenes Proyecto/instagram/Publicación Feria/1.png
