impatrq/Pleper/Imágenes Proyecto/instagram/Publicación Feria/2.png

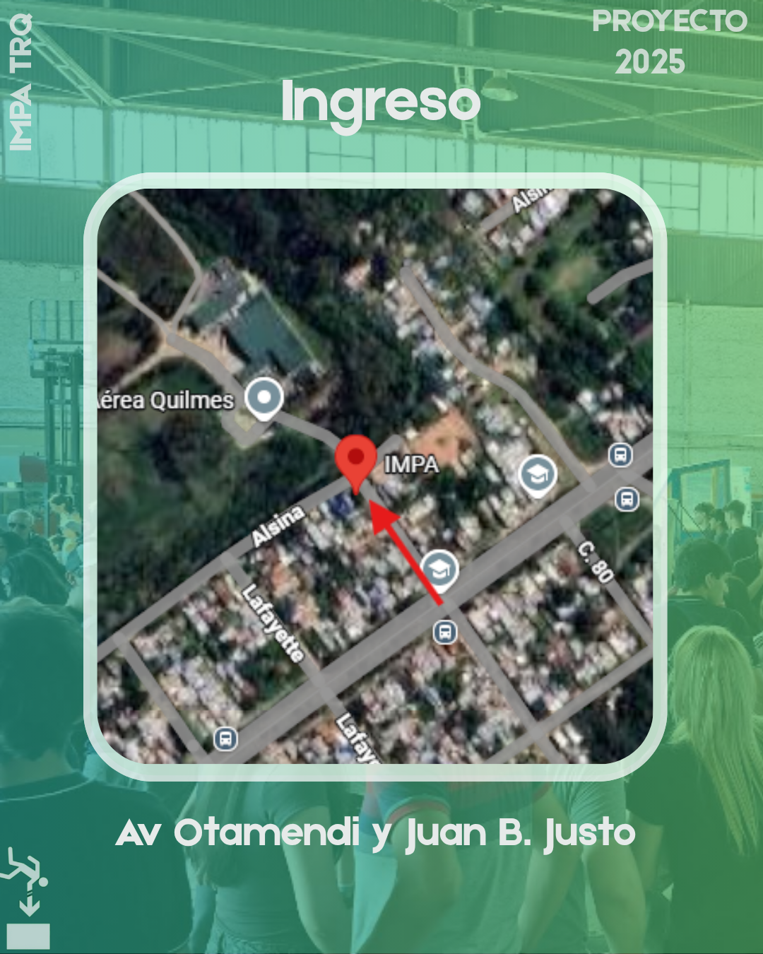
Imágenes Proyecto/instagram/Publicación Feria/2.png
