impatrq/Pleper/Imágenes Proyecto/Referencias/Capturas con Informacion/Informacion1.jpg

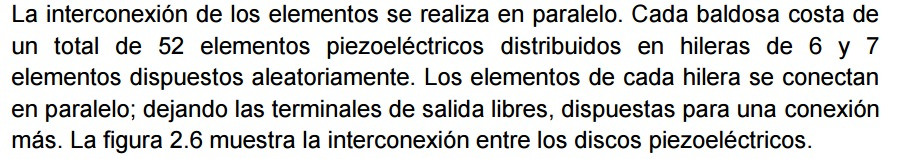
Imágenes Proyecto/Referencias/Capturas con Informacion/Informacion1.jpg
