impatrq/Pleper/Imágenes Proyecto/Referencias/Capturas con Informacion/Informacion2.jpg

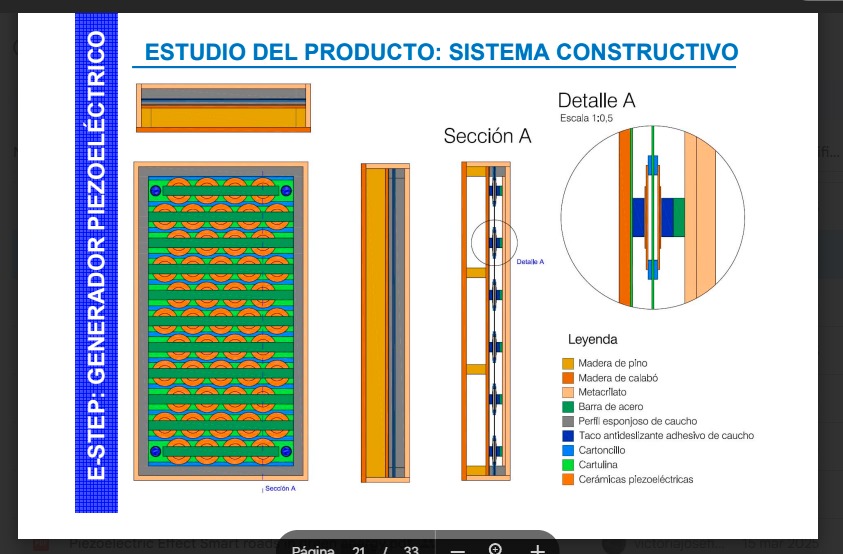
Imágenes Proyecto/Referencias/Capturas con Informacion/Informacion2.jpg
