impatrq/Pleper/Imágenes Proyecto/Referencias/Capturas con Informacion/Informacion3.jpg

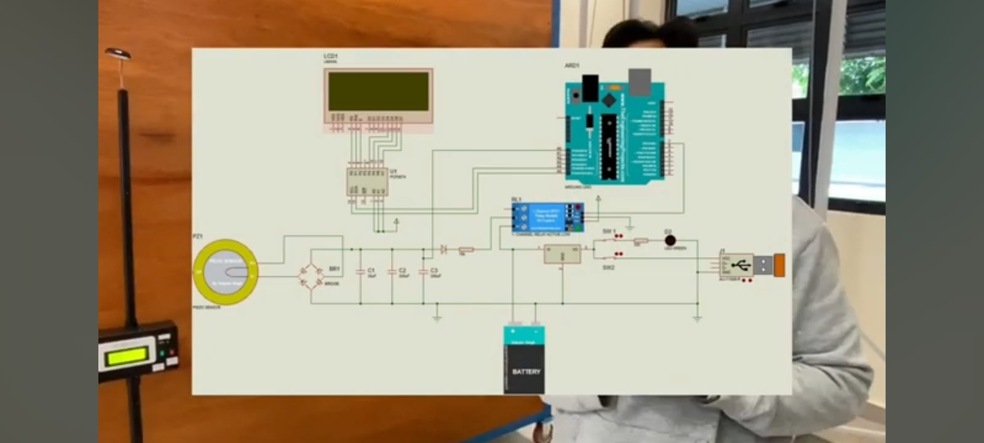
Imágenes Proyecto/Referencias/Capturas con Informacion/Informacion3.jpg
