impatrq/Pleper/Imágenes Proyecto/Referencias/Capturas con Informacion/Informacion4.jpg

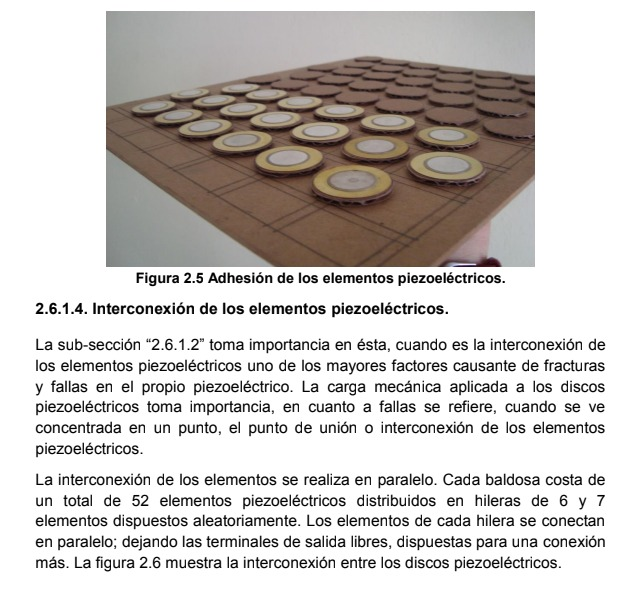
Imágenes Proyecto/Referencias/Capturas con Informacion/Informacion4.jpg
