impatrq/Pleper/Imágenes Proyecto/Referencias/Piezoléctrico Polarización.jpg

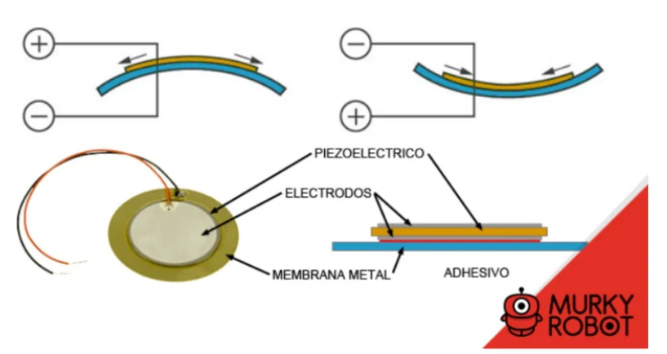
Imágenes Proyecto/Referencias/Piezoléctrico Polarización.jpg
