impatrq/Pleper/Imágenes Proyecto/Desarrollo/Componentes/Capacitores de 10000uF.jpg

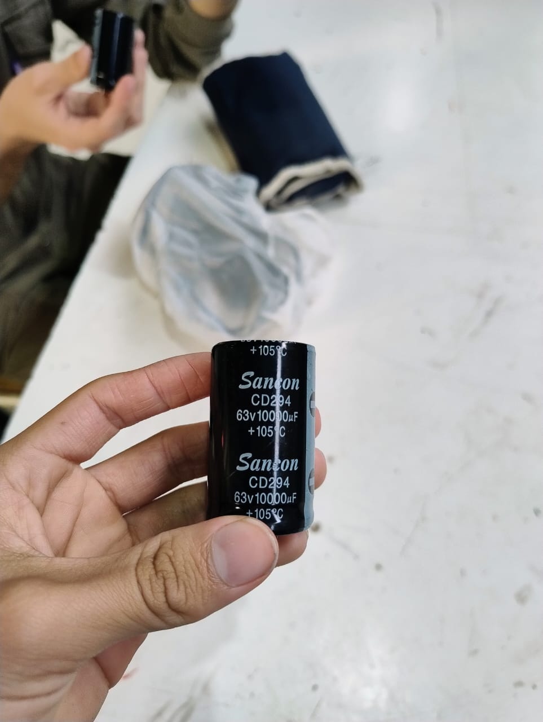
Imágenes Proyecto/Desarrollo/Componentes/Capacitores de 10000uF.jpg
