impatrq/Pleper/Imágenes Proyecto/Desarrollo/Componentes/Elementos de la baldosa.jpg

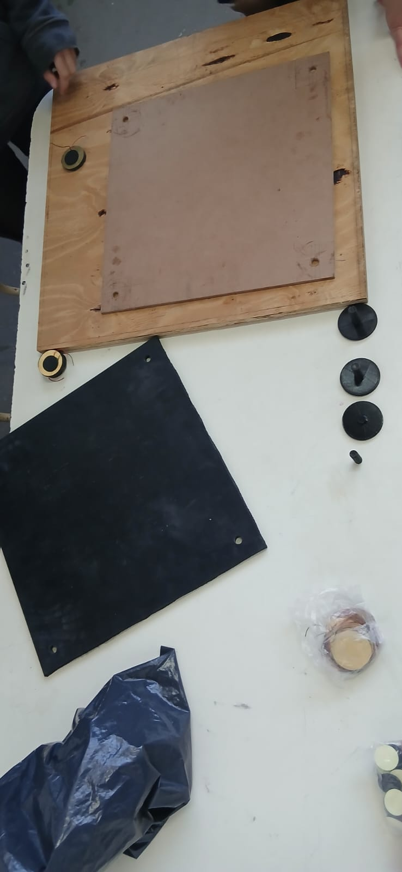
Imágenes Proyecto/Desarrollo/Componentes/Elementos de la baldosa.jpg
