impatrq/Pleper/Imágenes Proyecto/Desarrollo/Componentes/Imagen 16 topes canva.jpeg

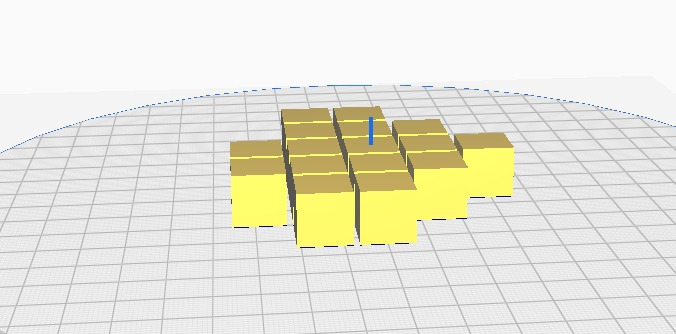
Imágenes Proyecto/Desarrollo/Componentes/Imagen 16 topes canva.jpeg
