impatrq/Pleper/Imágenes Proyecto/Desarrollo/Componentes/Imagen impresion 16 topes.jpeg

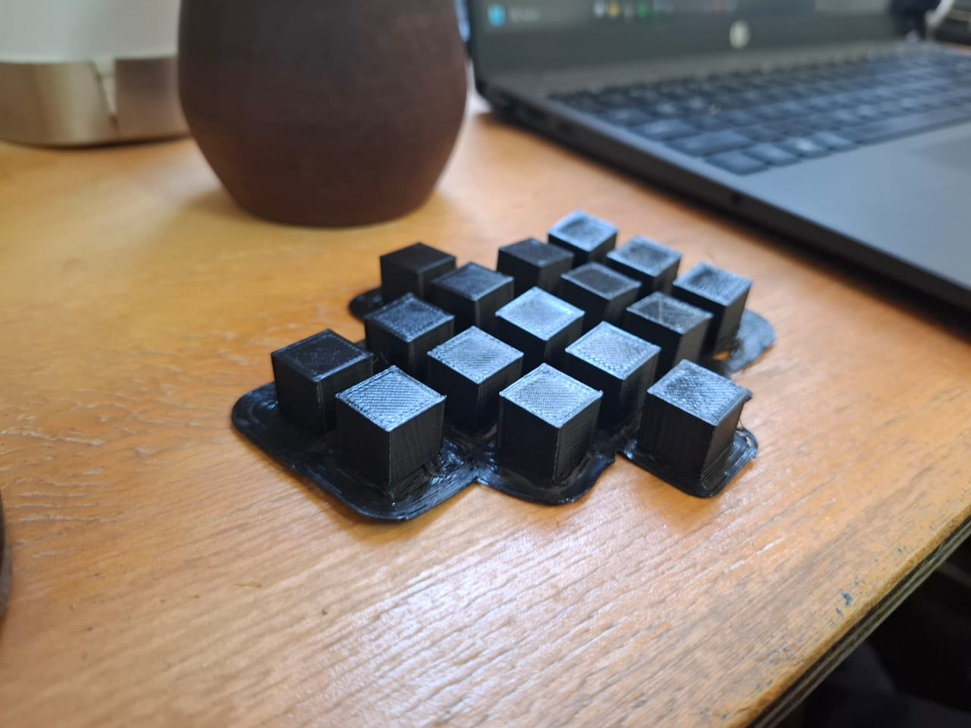
Imágenes Proyecto/Desarrollo/Componentes/Imagen impresion 16 topes.jpeg
