impatrq/Pleper/Imágenes Proyecto/Desarrollo/Componentes/Imagen remera detras.jpeg

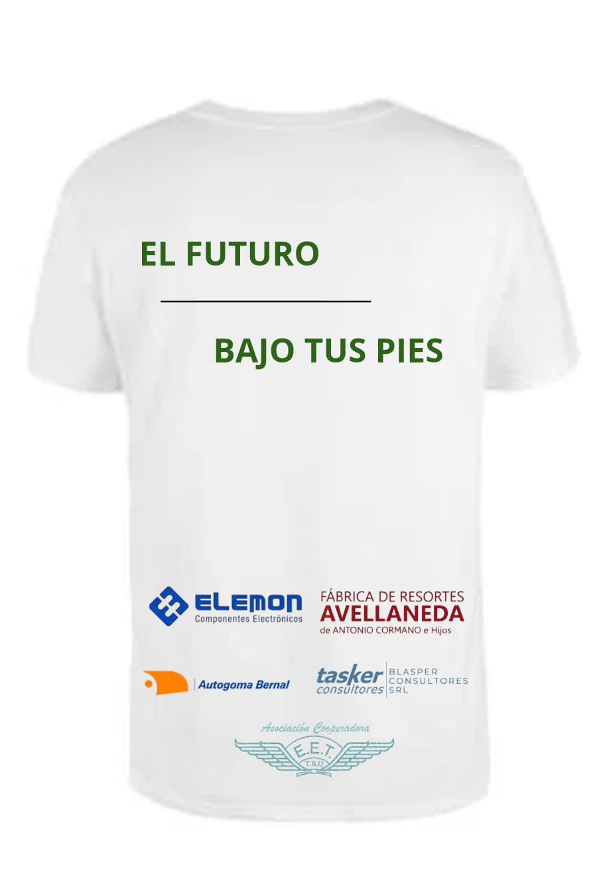
Imágenes Proyecto/Desarrollo/Componentes/Imagen remera detras.jpeg
