impatrq/Pleper/Imágenes Proyecto/Desarrollo/Componentes/Imagen remera frente.jpeg

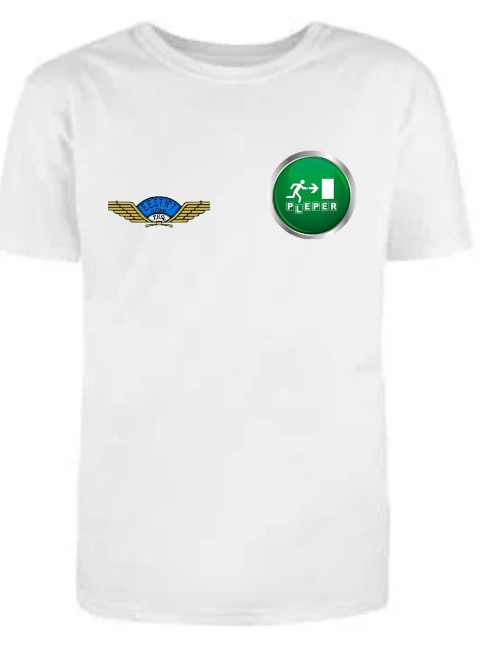
Imágenes Proyecto/Desarrollo/Componentes/Imagen remera frente.jpeg
