impatrq/Pleper/Imágenes Proyecto/Desarrollo/Componentes/Piezoeléctricos sobre la placa .jpg

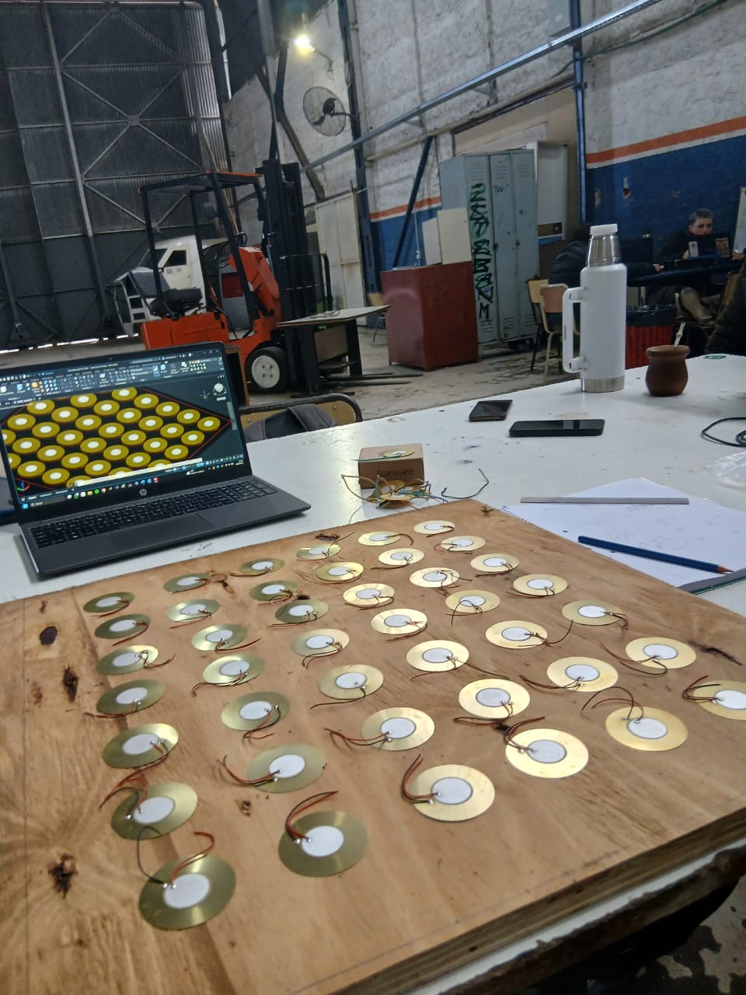
Imágenes Proyecto/Desarrollo/Componentes/Piezoeléctricos sobre la placa .jpg
