impatrq/Pleper/Imágenes Proyecto/Desarrollo/Componentes/Retirar la alfombra antideslizante de autogoma bernal.jpg

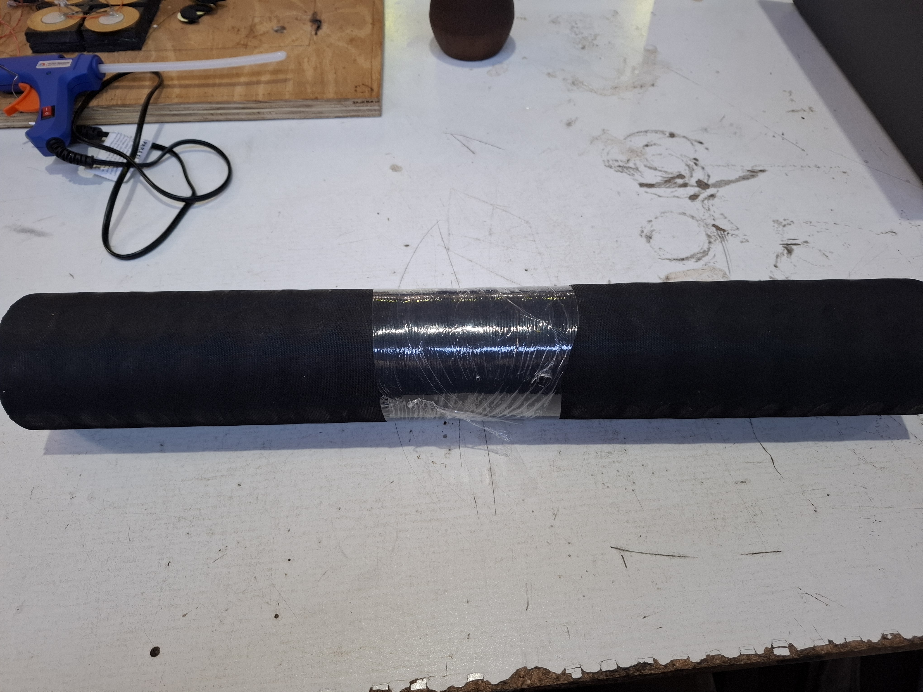
Imágenes Proyecto/Desarrollo/Componentes/Retirar la alfombra antideslizante de autogoma bernal.jpg
