impatrq/Pleper/Imágenes Proyecto/Desarrollo/Tareas manuales/2 soldados mas de los grupos a las borneras (2 y 5).jpg

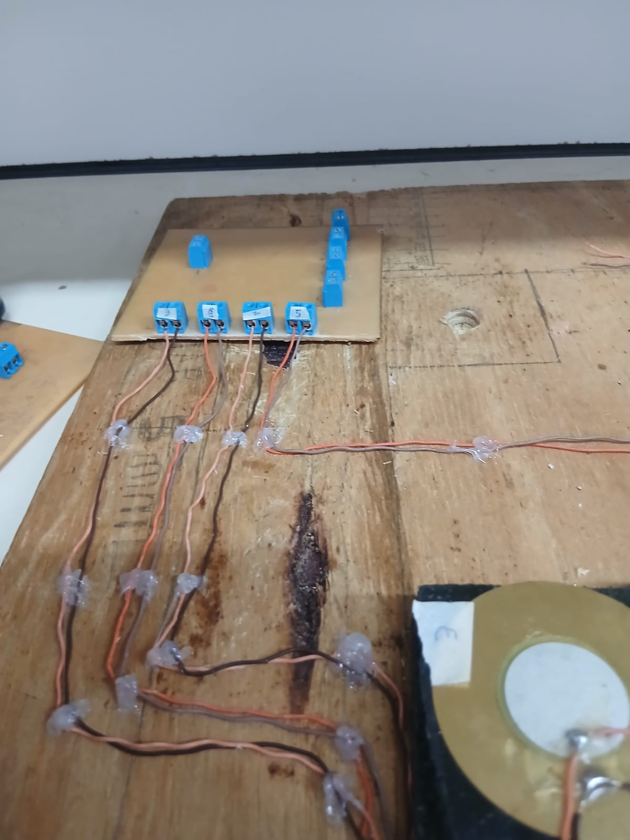
Imágenes Proyecto/Desarrollo/Tareas manuales/2 soldados mas de los grupos a las borneras (2 y 5).jpg
