impatrq/Pleper/Imágenes Proyecto/Desarrollo/Tareas manuales/Aplicación de cemento de contacto madera y caucho.jpg

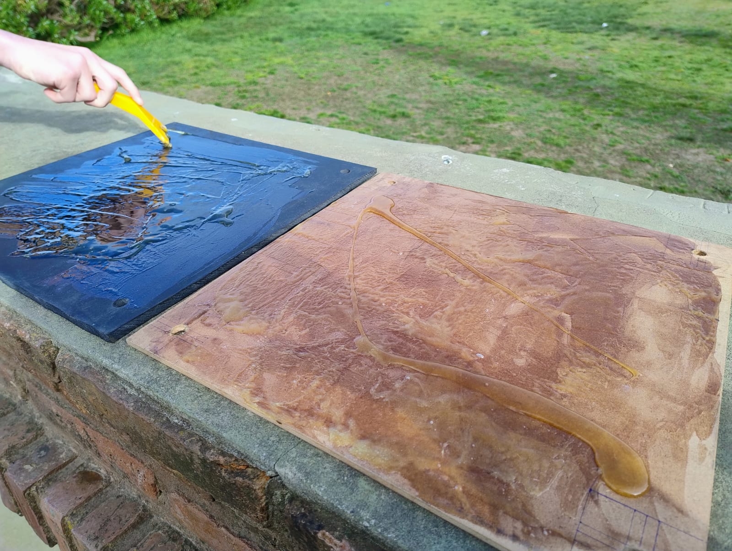
Imágenes Proyecto/Desarrollo/Tareas manuales/Aplicación de cemento de contacto madera y caucho.jpg
