impatrq/Pleper/Imágenes Proyecto/Desarrollo/Tareas manuales/Aplicación de cemento de contacto.jpg

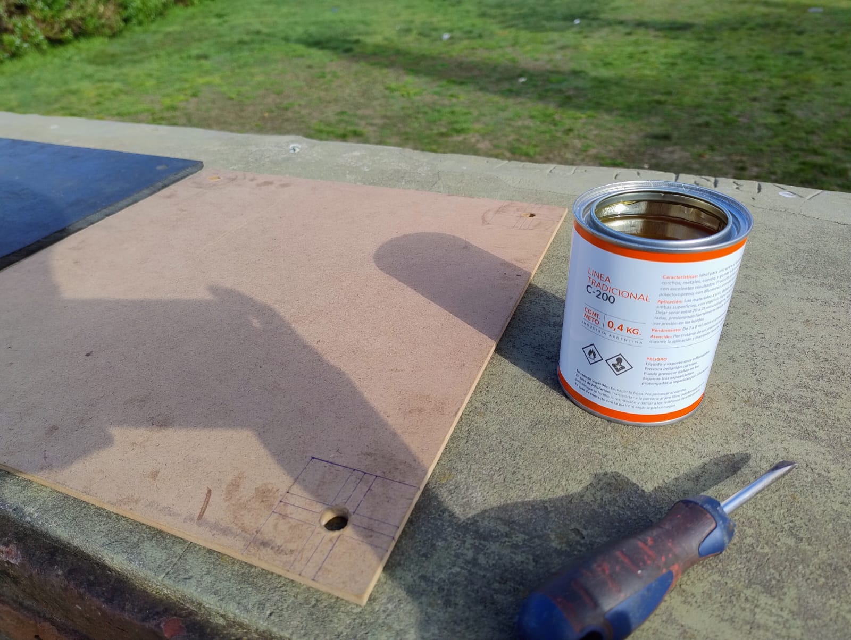
Imágenes Proyecto/Desarrollo/Tareas manuales/Aplicación de cemento de contacto.jpg
