impatrq/Pleper/Imágenes Proyecto/Desarrollo/Tareas manuales/Aplicando cemento de contacto.jpg

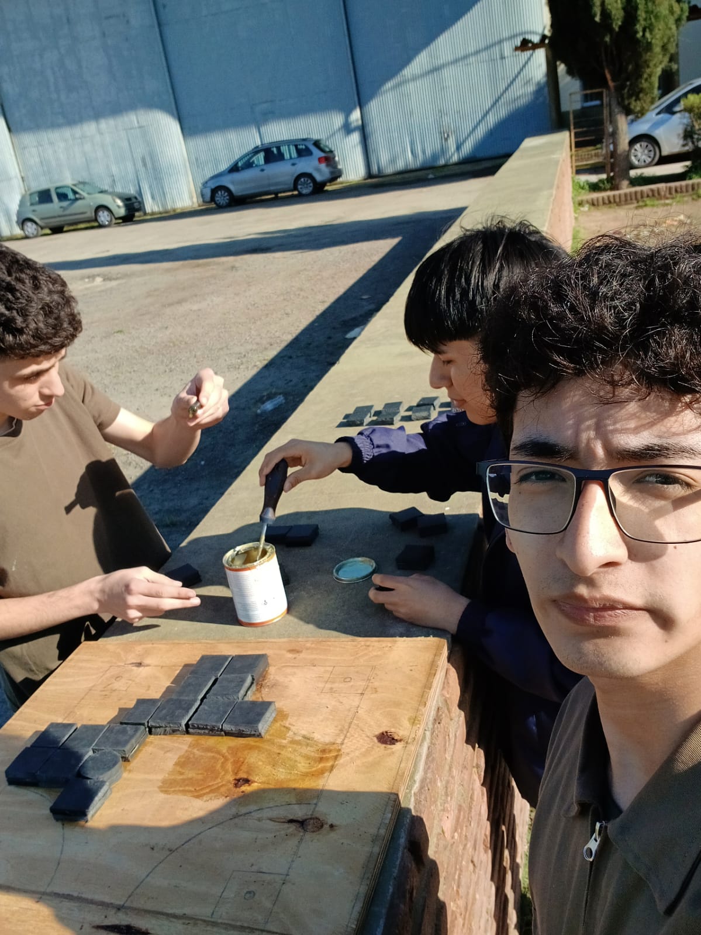
Imágenes Proyecto/Desarrollo/Tareas manuales/Aplicando cemento de contacto.jpg
