impatrq/Pleper/Imágenes Proyecto/Desarrollo/Tareas manuales/Cemento de contacto en los topes de caucho.jpg

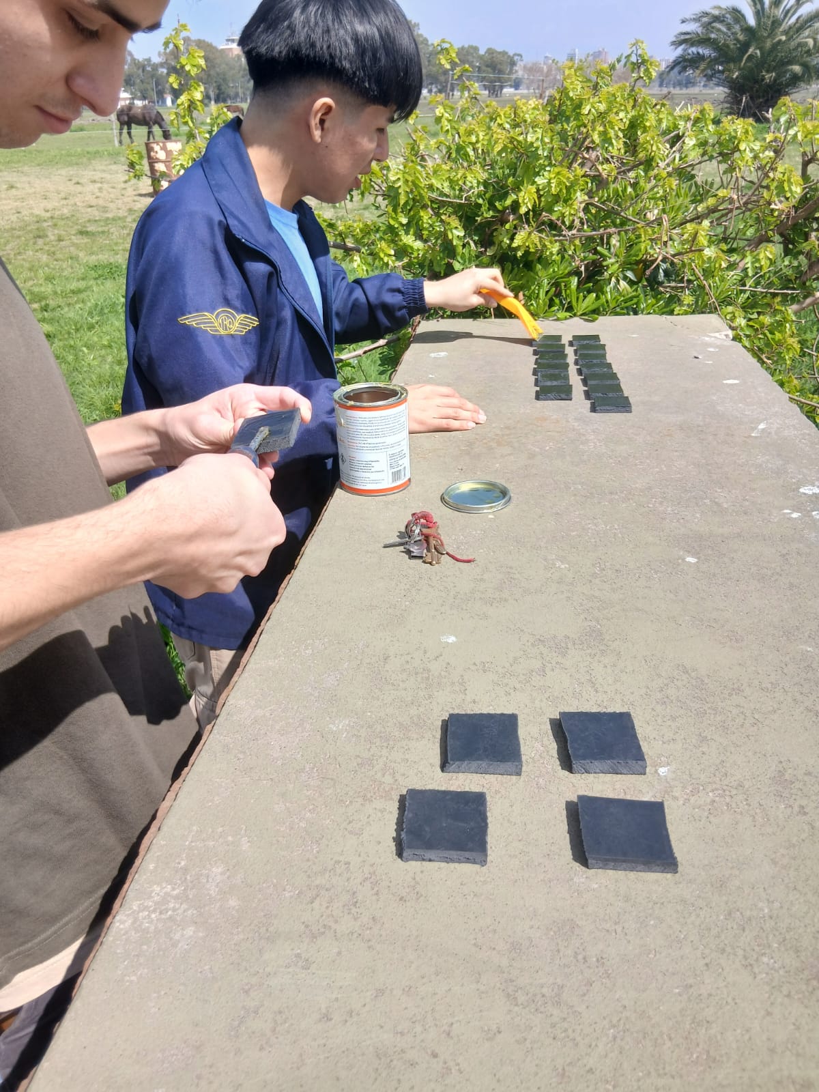
Imágenes Proyecto/Desarrollo/Tareas manuales/Cemento de contacto en los topes de caucho.jpg
