impatrq/Pleper/Imágenes Proyecto/Desarrollo/Tareas manuales/Cemento de contacto en los topes.jpg

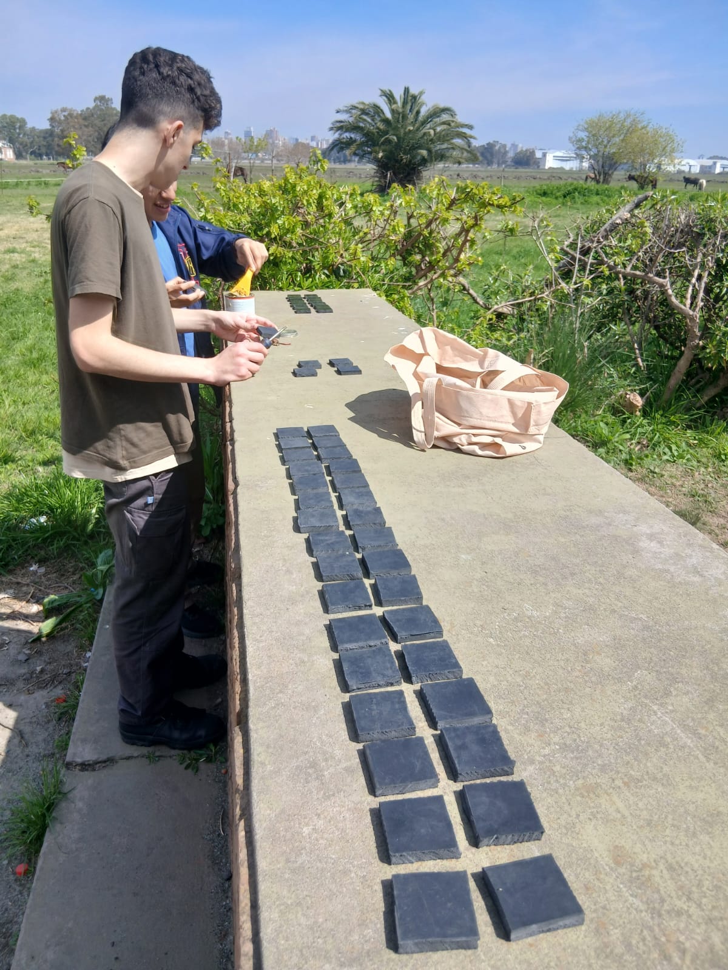
Imágenes Proyecto/Desarrollo/Tareas manuales/Cemento de contacto en los topes.jpg
