impatrq/Pleper/Imágenes Proyecto/Desarrollo/Tareas manuales/Conformando la distribución de piezoeléctricos sobre la baldosa.jpg

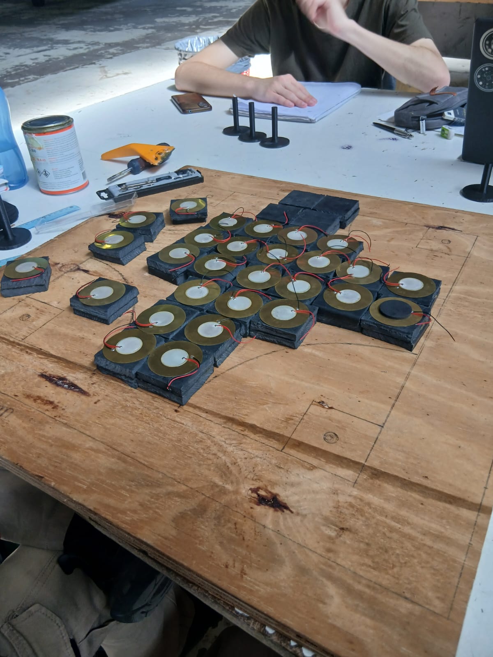
Imágenes Proyecto/Desarrollo/Tareas manuales/Conformando la distribución de piezoeléctricos sobre la baldosa.jpg
