impatrq/Pleper/Imágenes Proyecto/Desarrollo/Tareas manuales/Cortando caucho.jpg

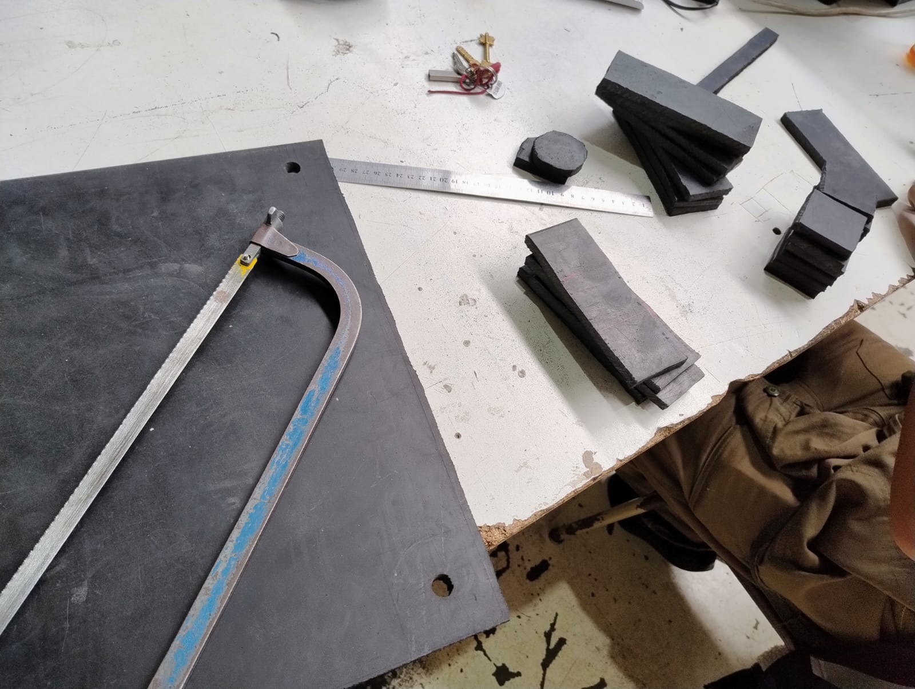
Imágenes Proyecto/Desarrollo/Tareas manuales/Cortando caucho.jpg
