impatrq/Pleper/Imágenes Proyecto/Desarrollo/Tareas manuales/Cortando el caucho a tamaño correspondiente.jpg

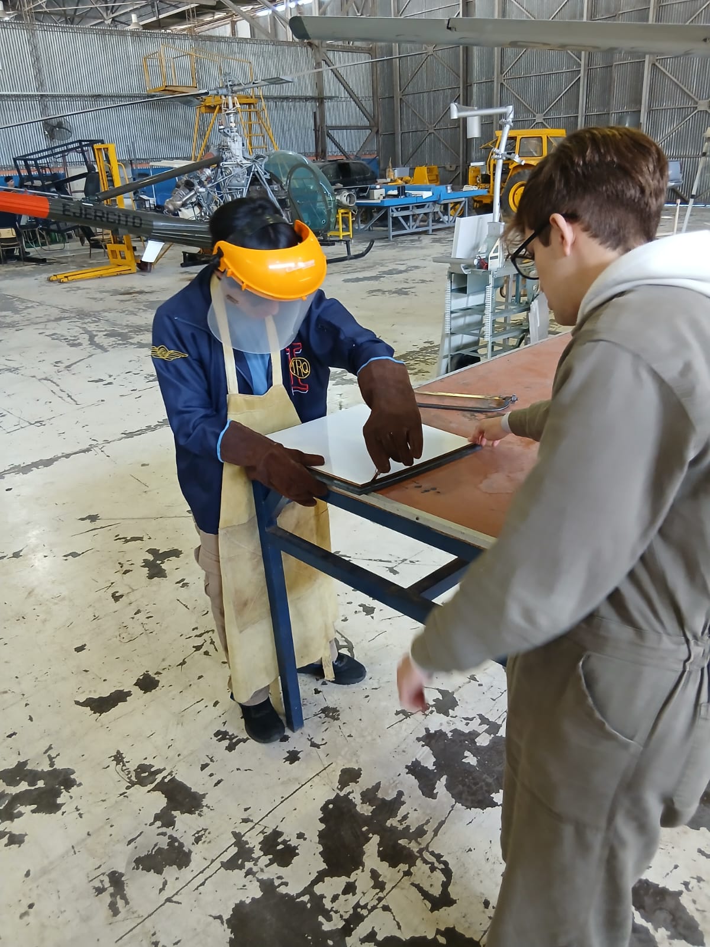
Imágenes Proyecto/Desarrollo/Tareas manuales/Cortando el caucho a tamaño correspondiente.jpg
