impatrq/Pleper/Imágenes Proyecto/Desarrollo/Tareas manuales/Cortando topes de caucho.jpg

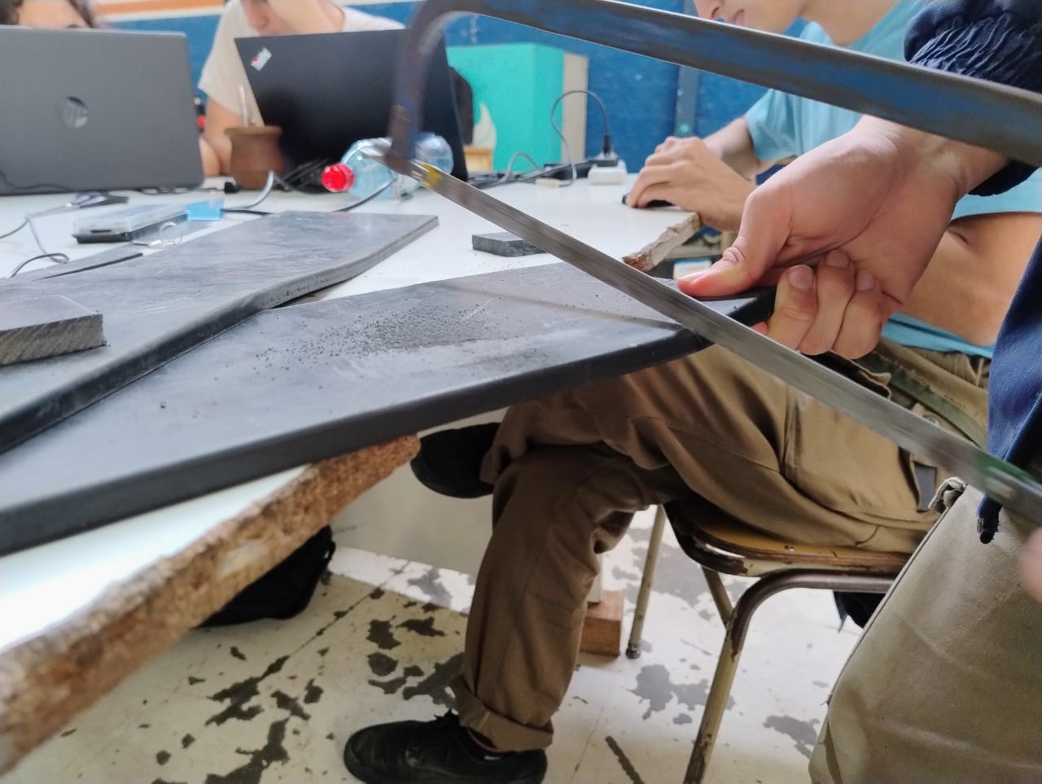
Imágenes Proyecto/Desarrollo/Tareas manuales/Cortando topes de caucho.jpg
