impatrq/Pleper/Imágenes Proyecto/Desarrollo/Tareas manuales/Cortar la alfombra antideslizante.jpg

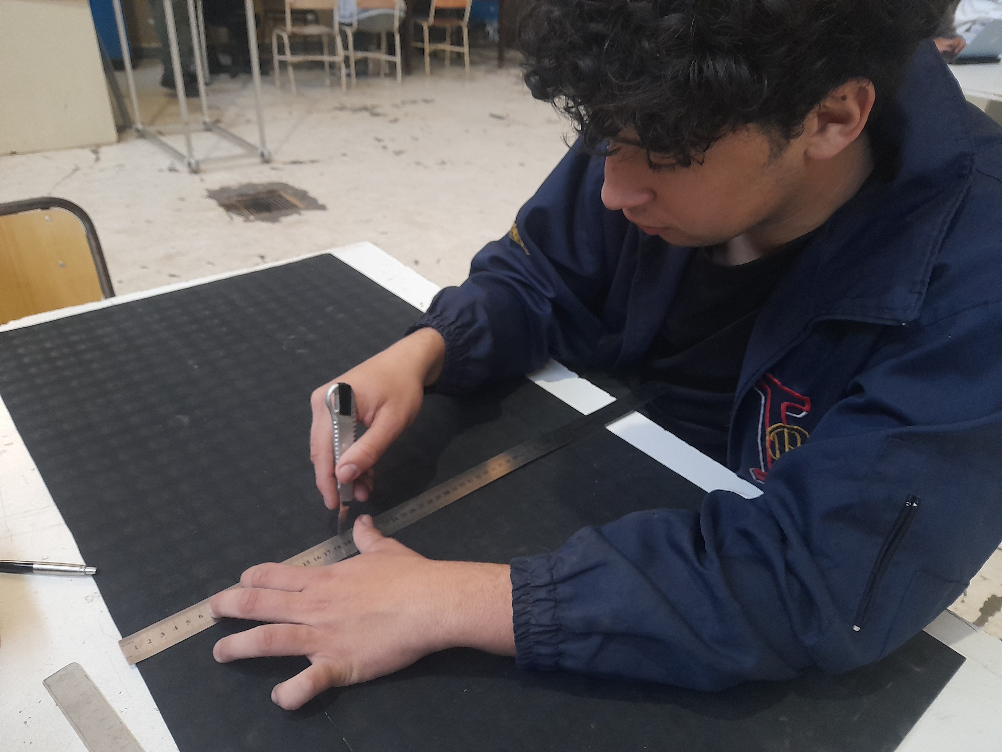
Imágenes Proyecto/Desarrollo/Tareas manuales/Cortar la alfombra antideslizante.jpg
