impatrq/Pleper/Imágenes Proyecto/Desarrollo/Tareas manuales/Corte de la alfombra de caucho para los topes.jpg

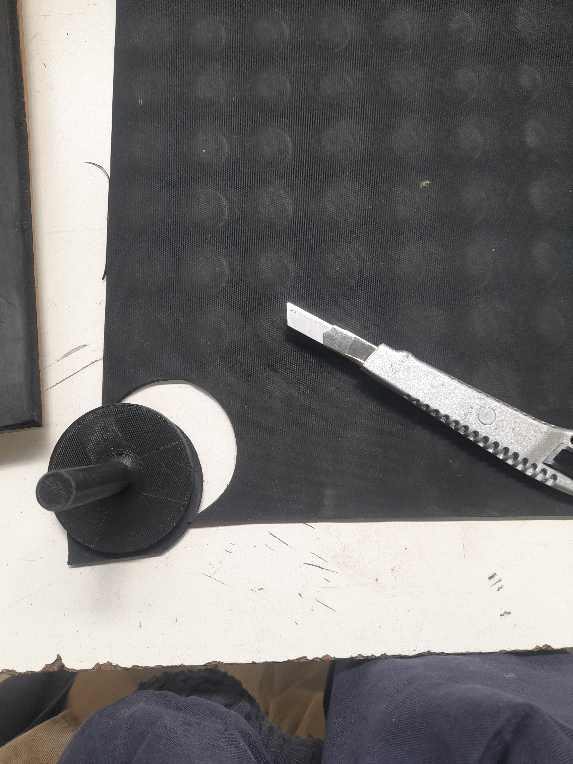
Imágenes Proyecto/Desarrollo/Tareas manuales/Corte de la alfombra de caucho para los topes.jpg
