impatrq/Pleper/Imágenes Proyecto/Desarrollo/Tareas manuales/Lijar el caucho para poder pegarlo con la alfombra.jpg

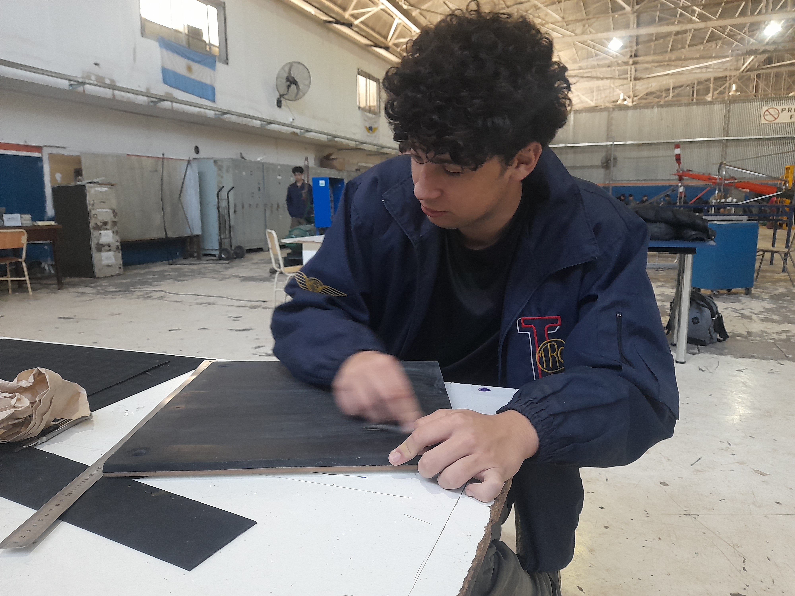
Imágenes Proyecto/Desarrollo/Tareas manuales/Lijar el caucho para poder pegarlo con la alfombra.jpg
