impatrq/Pleper/Imágenes Proyecto/Desarrollo/Tareas manuales/Probando la resistencia de los resortes.jpg

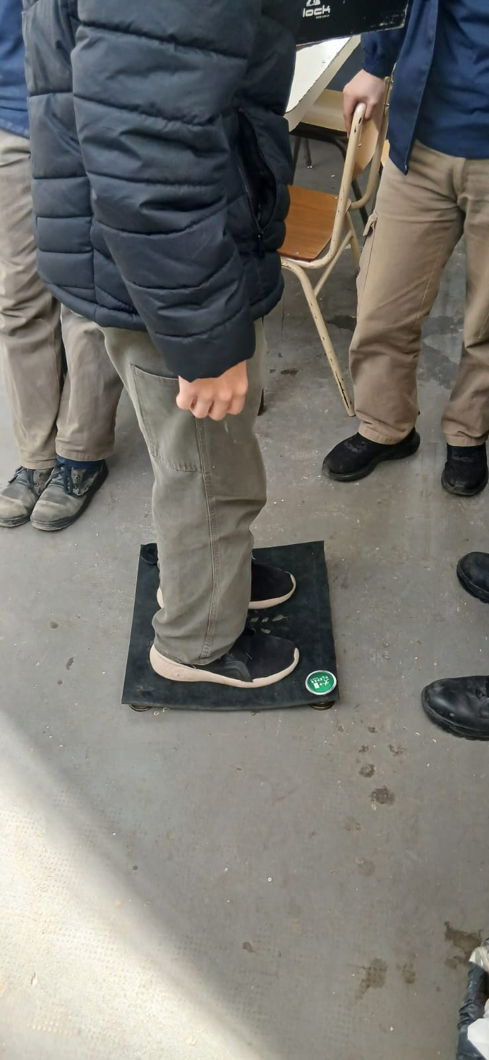
Imágenes Proyecto/Desarrollo/Tareas manuales/Probando la resistencia de los resortes.jpg
