impatrq/Pleper/Imágenes Proyecto/Desarrollo/Tareas manuales/Resoldado de los piezoelectricos despegados.jpg

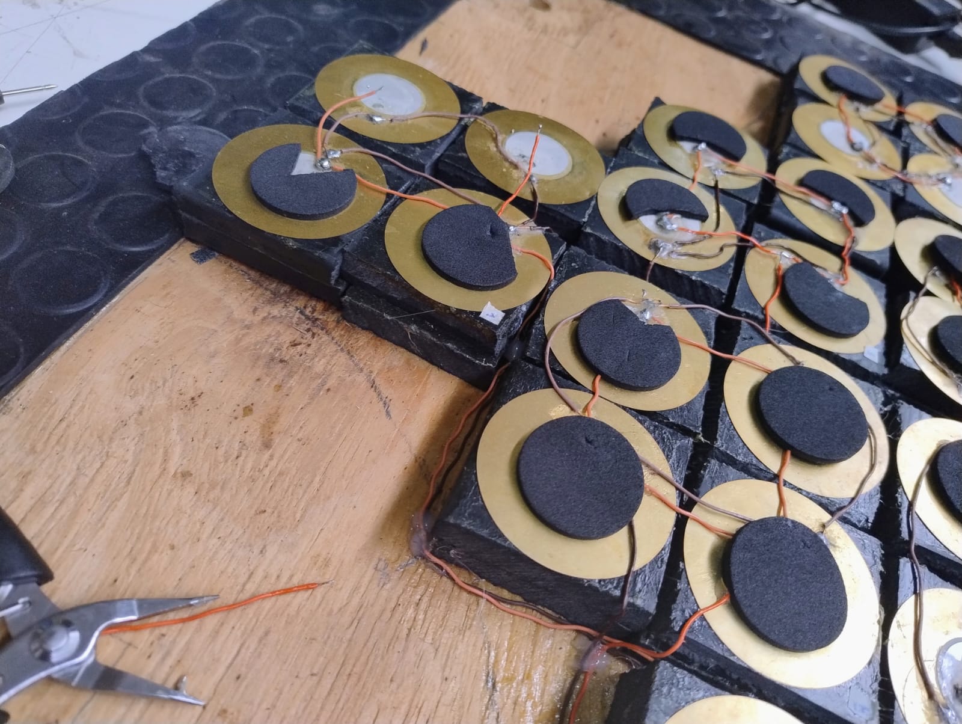
Imágenes Proyecto/Desarrollo/Tareas manuales/Resoldado de los piezoelectricos despegados.jpg
