impatrq/Pleper/Imágenes Proyecto/Desarrollo/Tareas manuales/Resoldado de los pines de la Raspberry Pi W.jpg

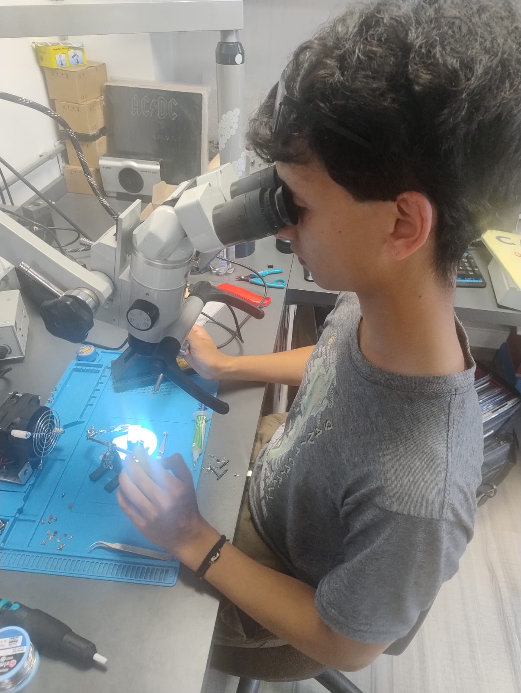
Imágenes Proyecto/Desarrollo/Tareas manuales/Resoldado de los pines de la Raspberry Pi W.jpg
