impatrq/Pleper/Imágenes Proyecto/Desarrollo/Tareas manuales/Pegado de los topes de goma a los piezoelectricos.jpg

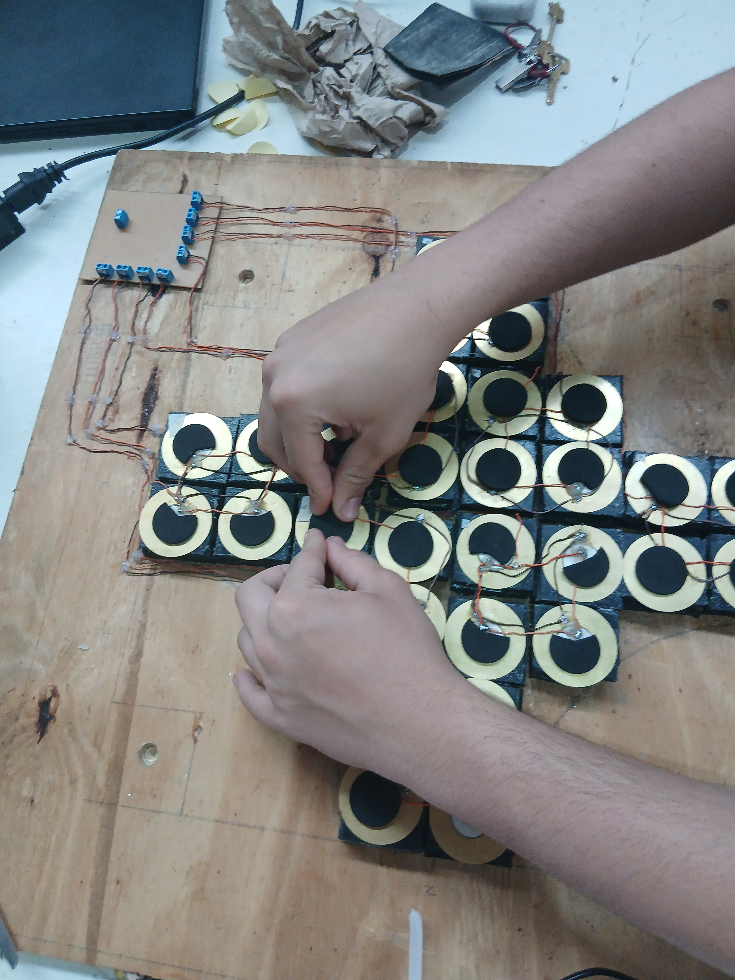
Imágenes Proyecto/Desarrollo/Tareas manuales/Pegado de los topes de goma a los piezoelectricos.jpg
