impatrq/Pleper/Imágenes Proyecto/Desarrollo/Imagen de placas/Prueba de funcionamiento del banco de capacitores.jpg

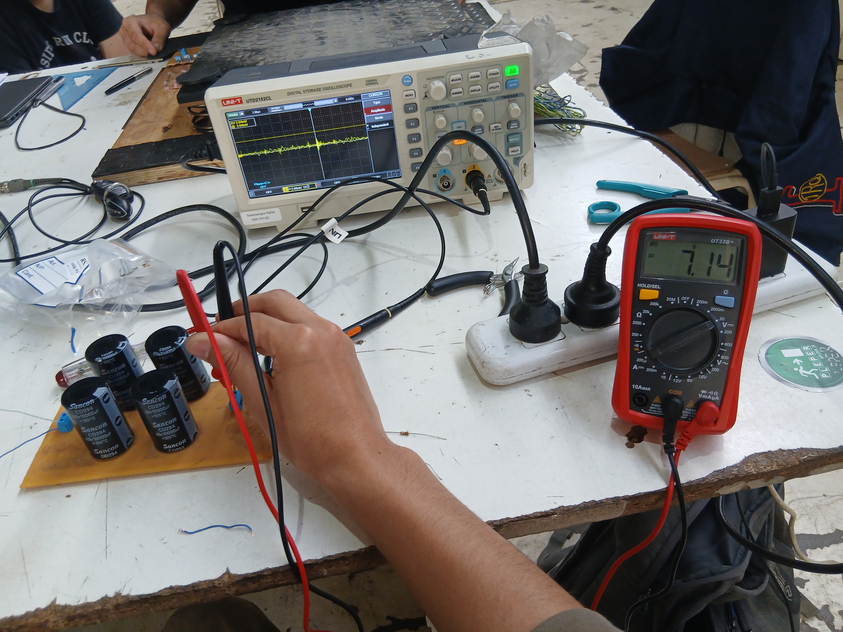
Imágenes Proyecto/Desarrollo/Imagen de placas/Prueba de funcionamiento del banco de capacitores.jpg
